petervflocke/ESP32Radio-V2PvF/Philips_DS1150/IMG20230203224731.jpg

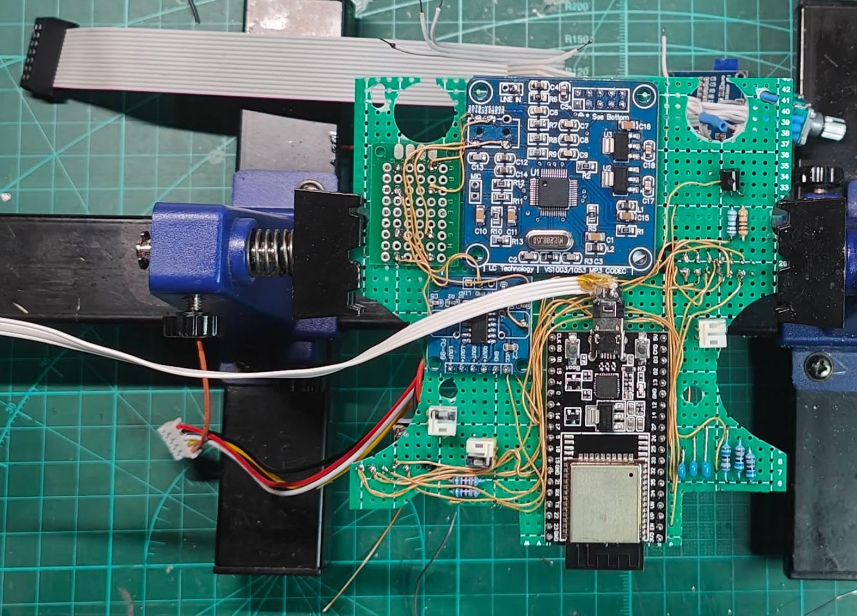
Philips_DS1150/IMG20230203224731.jpg
