petervflocke/ESP32Radio-V2PvF/Philips_DS1150/IMG20230203224739.jpg

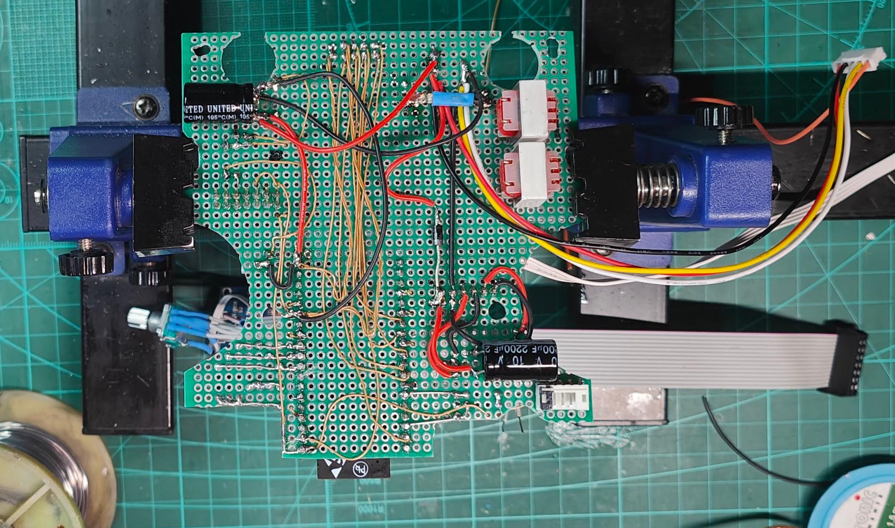
Philips_DS1150/IMG20230203224739.jpg
