petervflocke/ESP32Radio-V2PvF/Philips_DS1150/IMG20230204121923.jpg

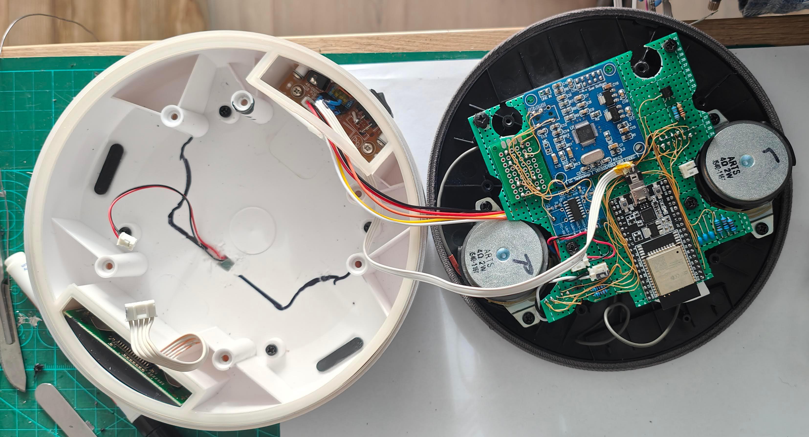
Philips_DS1150/IMG20230204121923.jpg
