petervflocke/ESP32Radio-V2PvF/Philips_DS1150/PhilipsESP32Radio.kicad_sch

## KiCad design Philips_DS1150/PhilipsESP32Radio.kicad_sch (2023-02-17)

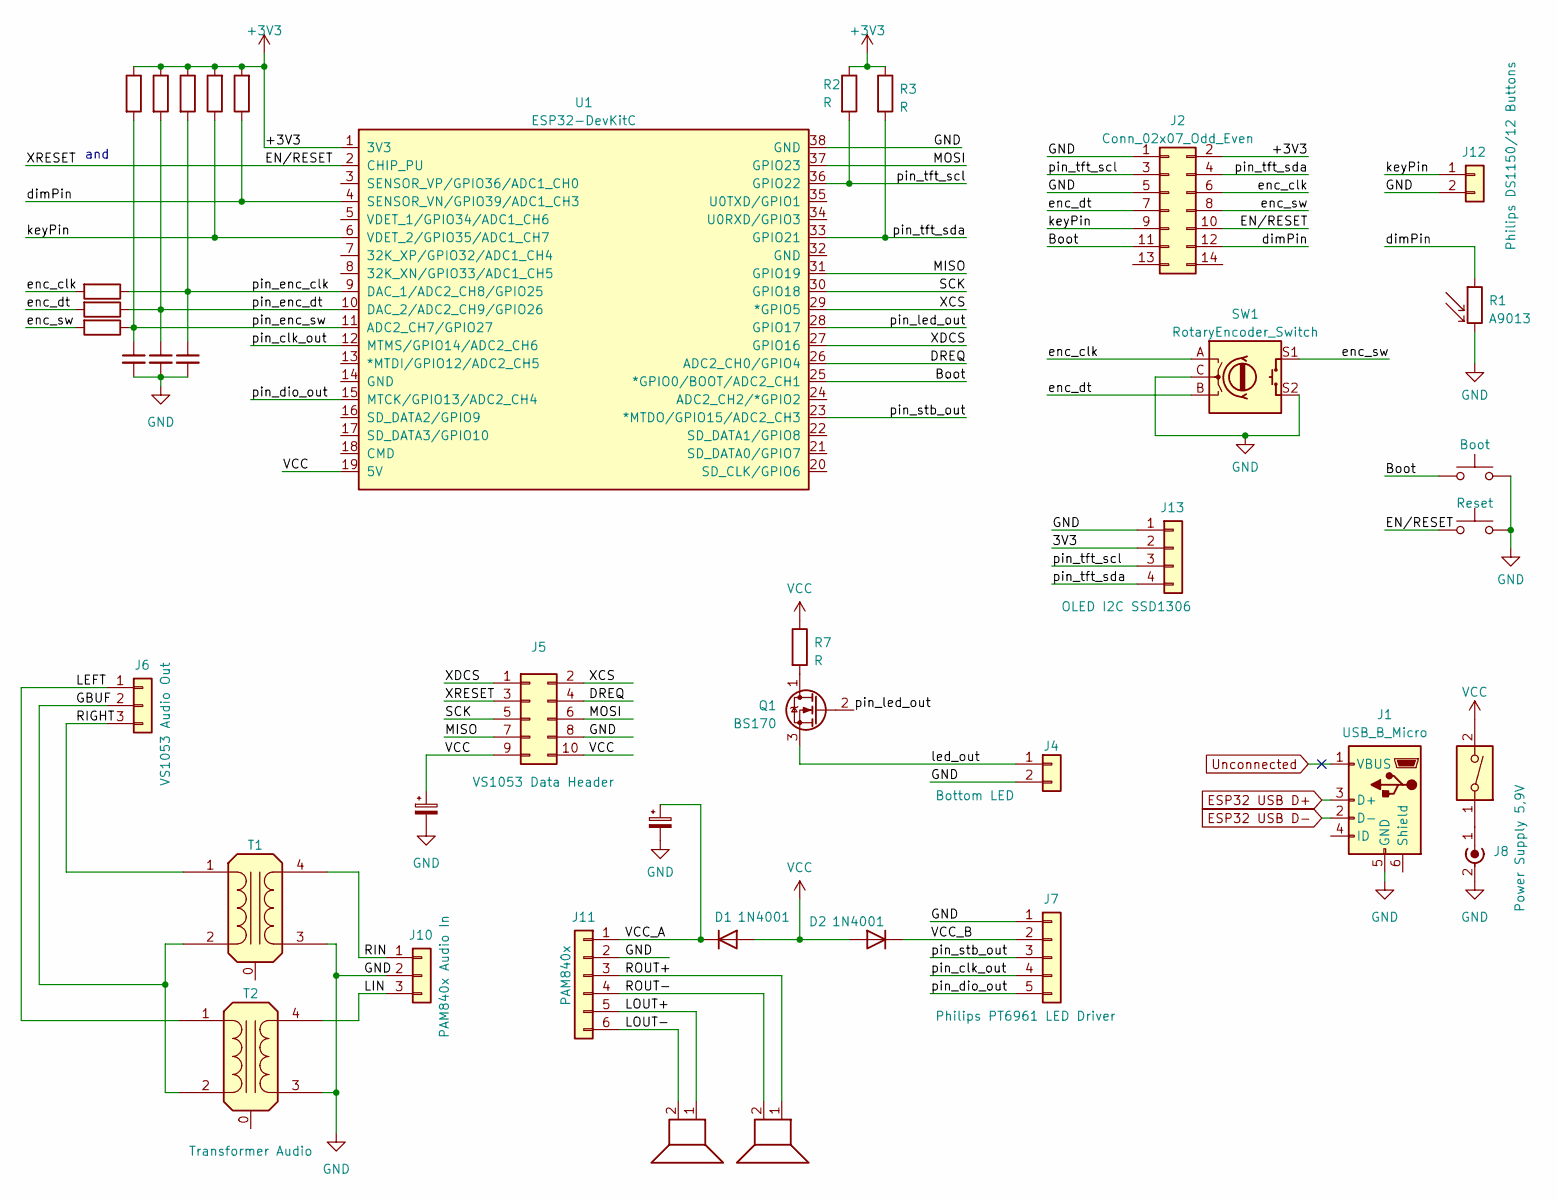
[picture p33: schematic PhilipsESP32Radio.kicad_sch]

Parts:
C1, C2, C3: C_Small
C4, C5: C_Polarized_Small
D1, D2: 1N4001; D_DO-41_SOD81_P10.16mm_Horizontal
J1: USB_B_Micro
J2: Conn_02x07_Odd_Even
J4: Bottom LED
J5: VS1053 Data Header
J6: VS1053 Audio Out
J7: Philips PT6961 LED Driver
J8: Power Supply 5,9V
J10: PAM840x Audio In
J11: PAM840x
J12: Philips DS1150/12 Buttons
J13: OLED I2C SSD1306
LS1, LS2: Speaker
Q1: BS170; TO-92_Inline
R1: A9013; R_LDR_5.0x4.1mm_P3mm_Vertical
R2, R3, R4, R5, R6, R7, R8, R9, R10, R11, R12: R
SW1: RotaryEncoder_Switch
SW2: Boot; SW_MEC_5GSH9
SW3: Reset; SW_MEC_5GSH9
SW4: SW_DIP_x01
T1: Transformer_Audio
T2: Transformer Audio
U1: ESP32-DevKitC

Connections:
3V3: J13.2
+3V3: J2.2, R2.1, R3.1, R8.2, R9.2, R10.1, R11.1, R12.1, U1.1 (3V3)
Boot: J2.11, SW2.1 (A), SW2.2 (A), U1.25 (*GPIO0/BOOT/ADC2_CH1)
DREQ: J5.4, U1.26 (ADC2_CH0/GPIO4)
EN/RESET: J2.10, J5.3, SW3.1 (A), SW3.2 (A), U1.2 (CHIP_PU)
ESP32 USB D+: J1.3 (D+)
ESP32 USB D-: J1.2 (D-)
GBUF: J6.2, T1.2 (AB), T2.2 (AB)
GND: C1.2, C2.2, C3.2, C4.2, C5.2, J1.5 (GND), J2.1, J2.5, J4.2, J5.8, J7.1, J8.2 (Ext), J10.2, J11.2, J12.2, J13.1, R1.2, SW1.C, SW1.S2, SW2.3 (B), SW2.4 (B), SW3.3 (B), SW3.4 (B), T1.3 (SA), T2.3 (SA), U1.38 (GND)
LEFT: J6.1, T2.1 (AA)
LIN: J10.3, T2.4 (SB)
LOUT+: J11.5, LS1.1
LOUT-: J11.6, LS1.2
MISO: J5.7, U1.31 (GPIO19)
MOSI: J5.6, U1.37 (GPIO23)
unnamed: J8.1 (In), SW4.1
unnamed: Q1.1 (D), R7.2
RIGHT: J6.3, T1.1 (AA)
RIN: J10.1, T1.4 (SB)
ROUT+: J11.3, LS2.1
ROUT-: J11.4, LS2.2
SCK: J5.5, U1.30 (GPIO18)
Unconnected: J1.1 (VBUS)
VCC: C5.1, D1.2 (A), D2.2 (A), J5.9, J5.10, R7.1, SW4.2, U1.19 (5V)
VCC_A: C4.1, D1.1 (K), J11.1
VCC_B: D2.1 (K), J7.2
XCS: J5.2, U1.29 (*GPIO5)
XDCS: J5.1, U1.27 (GPIO16)
dimPin: J2.12, R1.1, R9.1, U1.4 (SENSOR_VN/GPIO39/ADC1_CH3)
enc_clk: J2.6, R4.2, SW1.A
enc_dt: J2.7, R5.2, SW1.B
enc_sw: J2.8, R6.2, SW1.S1
keyPin: J2.9, J12.1, R8.1, U1.6 (VDET_2/GPIO35/ADC1_CH7)
led_out: J4.1, Q1.3 (S)
pin_clk_out: J7.4, U1.12 (MTMS/GPIO14/ADC2_CH6)
pin_dio_out: J7.5, U1.15 (MTCK/GPIO13/ADC2_CH4)
pin_enc_clk: C1.1, R4.1, R12.2, U1.9 (DAC_1/ADC2_CH8/GPIO25)
pin_enc_dt: C2.1, R5.1, R11.2, U1.10 (DAC_2/ADC2_CH9/GPIO26)
pin_enc_sw: C3.1, R6.1, R10.2, U1.11 (ADC2_CH7/GPIO27)
pin_led_out: Q1.2 (G), U1.28 (GPIO17)
pin_stb_out: J7.3
pin_stb_out: U1.23 (*MTDO/GPIO15/ADC2_CH3)
pin_tft_scl: J2.3, J13.3, R2.2, U1.36 (GPIO22)
pin_tft_sda: J2.4, J13.4, R3.2, U1.33 (GPIO21)

Notes on the sheet:
and
