petervflocke/ESP32Radio-V2PvF/src/main.cpp

//***************************************************************************************************
//*  ESP32_Radio V2 -- Webradio receiver for ESP32, VS1053 MP3 module and optional display.         *
//*                    By Ed Smallenburg.                                                           *
//***************************************************************************************************
// ESP32 libraries used:  See platformio.ini
// A library for the VS1053 (for ESP32) is not available (or not easy to find).  Therefore
// a class for this module is derived from the maniacbug library and integrated in this sketch.
// The Helix codecs for MP3 and HElix are taken from Wolle (schreibfaul1), see:
// https://github.com/schreibfaul1/ESP32-audioI2S
//
// See http://www.internet-radio.com for suitable stations.  Add the stations of your choice
// to the preferences through the webinterface.
// You may also use the "search" page of the webinterface to find stations.
//
// Brief description of the program:
// First a suitable WiFi network is found and a connection is made.
// Then a connection will be made to a shoutcast server.  The server starts with some
// info in the header in readable ascii, ending with a double CRLF, like:
//  icy-name:Classic Rock Florida - SHE Radio
//  icy-genre:Classic Rock 60s 70s 80s Oldies Miami South Florida
//  icy-url:http://www.ClassicRockFLorida.com
//  content-type:audio/mpeg
//  icy-pub:1
//  icy-metaint:32768          - Metadata after 32768 bytes of MP3-data
//  icy-br:128                 - in kb/sec (for Ogg this is like "icy-br=Quality 2"
//
// After de double CRLF is received, the server starts sending mp3- or Ogg-data.  For mp3, this
// data may contain metadata (non mp3) after every "metaint" mp3 bytes.
// The metadata is empty in most cases, but if any is available the content will be
// presented on the TFT.
// Pushing an input button causes the player to execute a programmable command.
//
// The display used is a Chinese 1.8 color TFT module 128 x 160 pixels.
// Now there is room for 26 characters per line and 16 lines.
// Software will work without installing the display.
// Other displays are also supported. See documentation.
// For configuration of the WiFi network(s): see the global data section further on.
//
// The VSPI interface is used for VS1053, TFT and SD.
//
// Wiring. Note that this is just an example.  Pins (except 18, 19 and 23 of the SPI interface)
// can be configured in the config page of the web interface.
//
// ESP32dev Signal  Wired to LCD        Wired to VS1053      AI Audio board    Wired to the rest
// -------- ------  --------------      -------------------  ---------------   ------------------------
// GPIO32           -                   pin 1 XDCS           I2C Clock
// GPIO33           -                   pin 1 XDCS           I2C Data
// GPIO5            -                   pin 2 XCS            KEY 6             -
// GPIO4            -                   pin 4 DREQ           AMPLIFIER_ENABLE  -
// GPIO2            pin 3 D/C or A0     -                    SPI_MISO          -
// GPIO16   RXD2    -                   -                                      TX of NEXTION (if in use)
// GPIO17   TXD2    -                   -                                      RX of NEXTION (if in use)
// GPIO18   SCK     pin 5 CLK or SCK    pin 5 SCK            KEY 5             -
// GPIO19   MISO    -                   pin 7 MISO           KEY 3             -
// GPIO23   MOSI    pin 4 DIN or SDA    pin 6 MOSI           KEY 4             -
// GPIO15           pin 2 CS            -                    SPI_MOSI          -
// GPIO3    RXD0    -                   -                                      Reserved serial input
// GPIO1    TXD0    -                   -                                      Reserved serial output
// GPIO34   -       -                   -                                      Optional pull-up resistor
// GPIO35   -       -                   -                                      Infrared receiver VS1838B
// GPIO25   -       -                   -                    I2S DSIN          Rotary encoder CLK
// GPIO26   -       -                   -                    I2S LRC           Rotary encoder DT
// GPIO27   -       -                   -                    I2S BCLK          Rotary encoder SW
// GPIO13   -       -                   -                    SD card CS        -
// GPIO14   -       -                   -                    SPI_SCK           -
// GPIO36   -       -                   -                    KEY 1             -
// GPIO13   -       -                   -                    KEY 2             -
// GPIO19   -       -                   -                    KEY 3             -
// GPIO23   -       -                   -                    KEY 4             -
// GPIO18   -       -                   -                    KEY 5             -
// GPIO05   -       -                   -                    KEY 6             -
// -------  ------  ---------------     -------------------                    ----------------
// GND      -       pin 8 GND           pin 8 GND                              Power supply GND
// VCC 5 V  -       pin 7 BL            -                                      Power supply
// VCC 5 V  -       pin 6 VCC           pin 9 5V                               Power supply
// EN       -       pin 1 RST           pin 3 XRST                             -
//
//  History:
//   Date     Author        Remarks
// ----------  --  ------------------------------------------------------------------
// 06-08-2021, ES: Copy from version 1.
// 06-08-2021, ES: Use SPIFFS and Async webserver.
// 23-08-2021, ES: Version with software MP3/AAC decoders.
// 05-10-2021, ES: Fixed internal DAC output, fixed OTA update.
// 06-10-2021, ES: Fixed AP mode.
// 10-02-2022, ES: Included ST7789 display.
// 11-02-2022, ES: SD card implementation.
// 26-03-2022, ES: Fixed NEXTION bug.
// 12-04-2022, ES: Fixed dataqueue bug (NEXT function).
// 13-04-2022, ES: Fixed redirect bug (preset was reset), fixed playlist.
// 14-04-2022, ES: Added posibility for a fixed WiFi network.
// 15-04-2022, ES: Redesigned station selection.
// 25-04-2022, ES: Support for WT32-ETH01 (wired Ethernet).
// 13-05-2022, ES: Correction I2S settings.
// 15-05-2022, ES: Correction mp3 list for web interface.
// 01-11-2022, ES: Support of AI Audio kit V2.1.
//
// Define the version number, the format used is the HTTP standard.
//#define VERSION     "Thu, 03 Nov 2022 13:00:00 GMT"     
#define VERSION "V2.1"                                    // just the PvF version
const char version[] = VERSION " " __DATE__;              // PvF prefers to have the last compilation time

#include <Arduino.h>                                      // Standard include for Platformio Arduino projects
#include <WiFi.h>
#include "config.h"                                       // Specify display type, decoder type
#include <nvs.h>                                          // Access to NVS
#include <PubSubClient.h>                                 // MTTQ access
#ifdef ETHERNET
  // Definitions for Ethernet controller
  #include <ETH.h>
  #define ETH_CLK_MODE    ETH_CLOCK_GPIO0_IN              // External clock from crystal oscillator
  #define ETH_TYPE        ETH_PHY_LAN8720                 // Type of controller
  #define ETH_ADDR        1                               // I2C address of Ethernet PHY
#else
  #include <WiFiMulti.h>                                  // Handle multiple WiFi networks
  WiFiMulti wifiMulti ;                                   // Object for WiFiMulti
#endif
#include <ESPmDNS.h>                                      // For multicast DNS
#include <time.h>                                         // Time functions
#include <SPI.h>                                          // For SPI handling
#include <ArduinoOTA.h>                                   // Over the air updates
#include <ESPAsyncWebServer.h>                            // For Async Web server
#include <freertos/queue.h>                               // FreeRtos queue support
#include <freertos/task.h>                                // FreeRtos task handling
#include <driver/adc.h>                                   // ADC driver
#include <base64.h>                                       // For Basic authentication
#include <SPIFFS.h>                                       // Filesystem
#include "utils.h"                                        // Some handy utilities

#ifdef FIDELO
  #include "fidelio_display.h"
  #define spiClk 1000000UL 
  #define dimPin 39
  #define keyPin 35
  #define NoAnalogButtonPressed 4000 /* actually 4095; maximum value ADC reading connected to 3.3V */
  
  FidelioDisplay fideDisplay;
#endif

/* Philips Fildelio Resistance Key Pin values measured with 3kohm pullup to 3.3v
1. clock :    0 -  100
2. +     :  470 -  530
3. light : 1060 - 1120
4. -     : 2220 - 2280
not pressed anything bigger then 2280
*/


#if defined(DEC_HELIX_INT) || defined(DEC_HELIX_AI)       // Software decoder using internal DAC?
  #define DEC_HELIX                                       // Yes, make sure to include software decoders
  #ifdef DEC_HELIX_AI                                     // AI Audio kit board?
   #include <AC101.h>
   #define GPIO_PA_EN 21                                  // GPIO for enabling amplifier
   AC101 dac ;                                            // AC101 controls
  #endif
#endif
#ifdef DEC_HELIX                                          // Software decoder?
  #include <driver/i2s.h>                                 // Driver for I2S output
  #include "mp3_decoder.h"                                // Yes, include libhelix_HMP3DECODER
  #include "aac_decoder.h"                                // and libhelix_HAACDECODER
  #include "helixfuncs.h"                                 // Helix functions
#else
  #include "VS1053.h"                                     // Driver for VS1053
#endif
#define FSIF              true                            // Format SPIFFS if not existing
#define QSIZ              400                             // Number of entries in the queue
#define NVSBUFSIZE        150                             // Max size of a string in NVS
// Access point name if connection to WiFi network fails.  Also the hostname for WiFi and OTA.
// Note that the password of an AP must be at least as long as 8 characters.
// Also used for other naming.
#ifndef NAME                                              // Name may be defined in config.h
  #define NAME            "ESP32-Radio"
#endif
#define MAXPRESETS        200                             // Max number of presets in preferences
#define MAXMQTTCONNECTS   5                               // Maximum number of MQTT reconnects before give-up
#define METASIZ           1024                            // Size of metaline buffer
#define MAXKEYS           200                             // Max. number of NVS keys in table
#define BL_TIME           45                              // Time-out [sec] for blanking TFT display (BL pin)
//
// Subscription topics for MQTT.  The topic will be pefixed by "PREFIX/", where PREFIX is replaced
// by the the mqttprefix in the preferences.  The next definition will yield the topic
// "ESP32Radio/command" if mqttprefix is "ESP32Radio".
#define MQTT_SUBTOPIC     "command"                      // Command to receive from MQTT
//
#define heapspace heap_caps_get_largest_free_block ( MALLOC_CAP_8BIT )

//**************************************************************************************************
// Forward declaration and prototypes of various functions.                                        *
//**************************************************************************************************
void        tftlog ( const char *str, bool newline = false ) ;
void        otastart() ;
void        showstreamtitle ( const char* ml, bool full = false ) ;
void        handlebyte_ch ( uint8_t b ) ;
void        handleCmd()  ;
const char* analyzeCmd ( const char* str ) ;
const char* analyzeCmd ( const char* par, const char* val ) ;
void        chomp ( String &str ) ;
String      nvsgetstr ( const char* key ) ;
bool        nvssearch ( const char* key ) ;
void        sdfuncs() ;
void        stop_mp3client () ;
void        tftset ( uint16_t inx, const char *str ) ;
void        tftset ( uint16_t inx, String& str ) ;
void        playtask ( void* parameter ) ;             // Task to play the stream on VS1053 or HELIX decoder
void        displayinfo ( uint16_t inx ) ;
void        gettime() ;
void        reservepin ( int8_t rpinnr ) ;
void        claimSPI ( const char* p ) ;                // Claim SPI bus for exclusive access
void        releaseSPI() ;                              // Release the claim
uint32_t    ssconv ( const uint8_t* bytes ) ;
void        scan_content_length ( const char* metalinebf ) ;
void        handle_notfound  ( AsyncWebServerRequest *request ) ;
void        handle_getprefs  ( AsyncWebServerRequest *request ) ;
void        handle_saveprefs ( AsyncWebServerRequest *request ) ;
void        handle_getdefs   ( AsyncWebServerRequest *request ) ;
void        handle_settings  ( AsyncWebServerRequest *request ) ;
void        handle_mp3list   ( AsyncWebServerRequest *request ) ;
String      readhostfrompref ( int16_t preset ) ;
void        displayStop();
bool        getPresetName (int16_t presetId, String &str);  // check if icy or preset name shall be used
#ifdef SCANANALOG
void        scananalog(); // scaning Philips
#endif


//**************************************************************************************************
// Several structs and enums.                                                                      *
//**************************************************************************************************
//

enum qdata_type { QDATA, QSTARTSONG, QSTOPSONG,       // datatyp in qdata_struct,
                  QSTOPTASK } ;
struct qdata_struct                                   // Data in queue for playtask (dataqueue)
{
  qdata_type                          datatyp ;       // Identifier
  __attribute__((aligned(4))) uint8_t buf[32] ;       // Buffer for chunk of mp3 data
} ;

struct ini_struct
{
  String         mqttbroker ;                         // The name of the MQTT broker server
  String         mqttprefix ;                         // Prefix to use for topics
  uint16_t       mqttport ;                           // Port, default 1883
  String         mqttuser ;                           // User for MQTT authentication
  String         mqttpasswd ;                         // Password for MQTT authentication
  uint8_t        reqvol ;                             // Requested volume
  uint8_t        rtone[4] ;                           // Requested bass/treble settings
  String         clk_server ;                         // Server to be used for time of day clock
  int8_t         clk_offset ;                         // Offset in hours with respect to UTC
  int8_t         clk_dst ;                            // Number of hours shift during DST
  int8_t         ir_pin ;                             // GPIO connected to output of IR decoder
  int8_t         enc_clk_pin ;                        // GPIO connected to CLK of rotary encoder
  int8_t         enc_dt_pin ;                         // GPIO connected to DT of rotary encoder
  int8_t         enc_sw_pin ;                         // GPIO connected to SW of rotary encoder / ZIPPY B5
  int8_t         enc_up_pin ;                         // GPIO connected to UP of ZIPPY B5 side switch
  int8_t         enc_dwn_pin ;                        // GPIO connected to DOWN of ZIPPY B5 side switch
  int8_t         tft_cs_pin ;                         // GPIO connected to CS of TFT screen
  int8_t         tft_dc_pin ;                         // GPIO connected to D/C or A0 of TFT screen
  int8_t         tft_scl_pin ;                        // GPIO connected to SCL of i2c TFT screen
  int8_t         tft_sda_pin ;                        // GPIO connected to SDA of I2C TFT screen
  int8_t         tft_bl_pin ;                         // GPIO to activate BL of display
  int8_t         tft_blx_pin ;                        // GPIO to activate BL of display (inversed logic)
  int8_t         nxt_rx_pin ;                         // GPIO for input from NEXTION
  int8_t         nxt_tx_pin ;                         // GPIO for output to NEXTION
  int8_t         sd_cs_pin ;                          // GPIO connected to CS of SD card
  int8_t         vs_cs_pin ;                          // GPIO connected to CS of VS1053
  int8_t         vs_dcs_pin ;                         // GPIO connected to DCS of VS1053
  int8_t         vs_dreq_pin ;                        // GPIO connected to DREQ of VS1053
  int8_t         shutdown_pin ;                       // GPIO to shut down the amplifier
  int8_t         shutdownx_pin ;                      // GPIO to shut down the amplifier (inversed logic)
  int8_t         spi_sck_pin ;                        // GPIO connected to SPI SCK pin
  int8_t         spi_miso_pin ;                       // GPIO connected to SPI MISO pin
  int8_t         spi_mosi_pin ;                       // GPIO connected to SPI MOSI pin
  int8_t         i2s_bck_pin ;                        // GPIO Pin number for I2S "BCK"
  int8_t         i2s_lck_pin ;                        // GPIO Pin number for I2S "L(R)CK"
  int8_t         i2s_din_pin ;                        // GPIO Pin number for I2S "DIN"
  int8_t         eth_mdc_pin ;                        // GPIO Pin number for Ethernet controller MDC
  int8_t         eth_mdio_pin ;                       // GPIO Pin number for Ethernet controller MDIO
  int8_t         eth_power_pin ;                      // GPIO Pin number for Ethernet controller POWER
  uint16_t       bat0 ;                               // ADC value for 0 percent battery charge
  uint16_t       bat100 ;                             // ADC value for 100 percent battery charge
  int8_t         pin_led_out;                         // PvF: GPIO out Pin for bottom LED driver
  int8_t         pin_stb_out;                         // PvF: GPIO out STB  Fidelo Display PT6964
  int8_t         pin_clk_out;                         // PvF: GPIO out CLK  Fidelo Display PT6964
  int8_t         pin_dio_out;                         // PvF: GPIO out DI/O Fidelo Display PT6964

} ;

struct WifiInfo_t                                     // For list with WiFi info
{
  char * ssid ;                                       // SSID for an entry
  char * passphrase ;                                 // Passphrase for an entry
} ;

struct nvs_entry
{
  uint8_t  Ns ;                                       // Namespace ID
  uint8_t  Type ;                                     // Type of value
  uint8_t  Span ;                                     // Number of entries used for this item
  uint8_t  Rvs ;                                      // Reserved, should be 0xFF
  uint32_t CRC ;                                      // CRC
  char     Key[16] ;                                  // Key in Ascii
  uint64_t Data ;                                     // Data in entry
} ;

struct nvs_page                                       // For nvs entries
{ // 1 page is 4096 bytes
  uint32_t  State ;
  uint32_t  Seqnr ;
  uint32_t  Unused[5] ;
  uint32_t  CRC ;
  uint8_t   Bitmap[32] ;
  nvs_entry Entry[126] ;
} ;

struct keyname_t                                      // For keys in NVS
{
  char      Key[16] ;                                 // Max length is 15 plus delimeter
} ;

// Preset info
enum station_state_t { ST_PRESET, ST_REDIRECT,        // Possible preset status
                       ST_PLAYLIST, ST_STATION } ;
struct preset_info_t
{
    int16_t            preset ;                       // Preset to play
    int16_t            highest_preset ;               // Highest possible preset
    station_state_t    station_state ;                // Station state
    int16_t            playlistnr ;                   // Index in playlist
    int16_t            highest_playlistnr ;           // Highest possible preset
    String             playlisthost ;                 // Host with playlist
    String             host ;                         // Resulting host
} ;


//**************************************************************************************************
// Global data section.                                                                            *
//**************************************************************************************************
// There is a block ini-data that contains some configuration.  Configuration data is              *
// saved in the preferences by the webinterface.  On restart the new data will                     *
// de read from these preferences.                                                                 *
// Items in ini_block can be changed by commands from webserver/MQTT/Serial.                       *
//**************************************************************************************************

enum datamode_t { INIT = 0x1, HEADER = 0x2, DATA = 0x4,      // State for datastream
                  METADATA = 0x8, PLAYLISTINIT = 0x10,
                  PLAYLISTHEADER = 0x20, PLAYLISTDATA = 0x40,
                  STOPREQD = 0x80, STOPPED = 0x100
                } ;

// Global variables
int               numSsid ;                              // Number of available WiFi networks
bool              ota = true ;                           // Allow OTA updates
preset_info_t     presetinfo ;                           // Info about the current or new station
ini_struct        ini_block ;                            // Holds configurable data
AsyncWebServer    cmdserver ( 80 ) ;                     // Instance of embedded webserver, port 80
AsyncClient*      mp3client = NULL ;                     // An instance of the mp3 client
WiFiClient        wmqttclient ;                          // An instance for mqtt
PubSubClient      mqttclient ( wmqttclient ) ;           // Client for MQTT subscriber
TaskHandle_t      maintask ;                             // Taskhandle for main task
TaskHandle_t      xplaytask ;                            // Task handle for playtask
SemaphoreHandle_t SPIsem = NULL ;                        // For exclusive SPI usage
hw_timer_t*       timer = NULL ;                         // For timer
char              timetxt[9] ;                           // Converted timeinfo
char              cmd[130] ;                             // Command from MQTT or Serial
const qdata_type  stopcmd = QSTOPSONG ;                  // Command for radio/SD
const qdata_type  startcmd = QSTARTSONG ;                // Command for radio/SD
QueueHandle_t     radioqueue = 0 ;                       // Queue for icecast commands
QueueHandle_t     dataqueue = 0 ;                        // Queue for mp3 datastream
QueueHandle_t     sdqueue = 0 ;                          // For commands to sdfuncs
qdata_struct      outchunk ;                             // Data to queue
qdata_struct      inchunk ;                              // Data from queue
uint8_t*          outqp = outchunk.buf ;                 // Pointer to buffer in outchunk
uint32_t          totalcount = 0 ;                       // Counter mp3 data
datamode_t        datamode ;                             // State of datastream
int               metacount ;                            // Number of bytes in metadata
int               datacount ;                            // Counter databytes before metadata
char              metalinebf[METASIZ + 1] ;              // Buffer for metaline/ID3 tags
int16_t           metalinebfx ;                          // Index for metalinebf
String            icystreamtitle ;                       // Streamtitle from metadata
String            icyname ;                              // Icecast station name
String            audio_ct ;                             // Content-type, like "audio/aacp"
String            ipaddress ;                            // Own IP-address
int               bitrate ;                              // Bitrate in kb/sec
int               mbitrate ;                             // Measured bitrate
int               metaint = 0 ;                          // Number of databytes between metadata
bool              reqtone = false ;                      // New tone setting requested
bool              muteflag = false ;                     // Mute output
bool              resetreq = false ;                     // Request to reset the ESP32
bool              testreq = false ;                      // Request to print test info
bool              eth_connected = false ;                // Ethernet connected or not
bool              NetworkFound = false ;                 // True if WiFi network connected
bool              mqtt_on = false ;                      // MQTT in use
String            networks = "None|" ;                   // Found networks in the surrounding
uint16_t          mqttcount = 0 ;                        // Counter MAXMQTTCONNECTS
int8_t            playingstat = 0 ;                      // 1 if radio is playing (for MQTT)
int16_t           playlist_num = 0 ;                     // Nonzero for selection from playlist
bool              chunked = false ;                      // Station provides chunked transfer
int               chunkcount = 0 ;                       // Counter for chunked transfer
uint16_t          ir_value = 0 ;                         // IR code
uint32_t          ir_0 = 550 ;                           // Average duration of an IR short pulse
uint32_t          ir_1 = 1650 ;                          // Average duration of an IR long pulse
struct tm         timeinfo ;                             // Will be filled by NTP server
bool              time_req = false ;                     // Set time requested
uint16_t          adcvalraw ;                            // ADC value (raw)
uint16_t          adcval ;                               // ADC value (battery voltage, averaged)
uint32_t          clength ;                              // Content length found in http header
uint16_t          bltimer = 0 ;                          // Backlight time-out counter
bool              dsp_ok = false ;                       // Display okay or not
int               ir_intcount = 0 ;                      // For test IR interrupts
bool              spftrigger = false ;                   // To trigger execution of special functions
const char*       fixedwifi = "" ;                       // Used for FIXEDWIFI option
const esp_partition_t*  spiffs = NULL ;                  // Pointer to SPIFFS partition struct
std::vector<WifiInfo_t> wifilist ;                       // List with wifi_xx info

// nvs stuff
nvs_page                nvsbuf ;                         // Space for 1 page of NVS info
const esp_partition_t*  nvs ;                            // Pointer to partition struct
esp_err_t               nvserr ;                         // Error code from nvs functions
uint32_t                nvshandle = 0 ;                  // Handle for nvs access
uint8_t                 namespace_ID ;                   // Namespace ID found
char                    nvskeys[MAXKEYS][16] ;           // Space for NVS keys
std::vector<keyname_t>  keynames ;                       // Keynames in NVS

// Rotary encoder stuff
#define sv DRAM_ATTR static volatile
sv uint16_t       clickcount = 0 ;                       // Incremented per encoder click
sv int16_t        rotationcount = 0 ;                    // Current position of rotary switch
sv uint16_t       enc_inactivity = 0 ;                   // Time inactive
sv bool           singleclick = false ;                  // True if single click detected
sv bool           doubleclick = false ;                  // True if double click detected
sv bool           tripleclick = false ;                  // True if triple click detected
sv bool           longclick = false ;                    // True if longclick detected
enum enc_menu_t { VOLUME, PRESET, TRACK };    // State for rotary encoder menu, OFF for new toggle comand
enc_menu_t        enc_menu_mode = VOLUME ;               // Default is VOLUME mode

//
struct progpin_struct                                    // For programmable input pins
{
  int8_t         gpio ;                                  // Pin number
  bool           reserved ;                              // Reserved for connected devices
  bool           avail ;                                 // Pin is available for a command
  String         command ;                               // Command to execute when activated
                                                         // Example: "uppreset=1"
  bool           cur ;                                   // Current state, true = HIGH, false = LOW
} ;

progpin_struct   progpin[] =                             // Input pins and programmed function
{
  {  0, false, false,  "", false },
  //{  1, true,  false,  "", false },                    // Reserved for TX Serial output
  {  2, false, false,  "", false },
  //{  3, true,  false,  "", false },                    // Reserved for RX Serial input
  {  4, false, false,  "", false },
  {  5, false, false,  "", false },
  //{  6, true,  false,  "", false },                    // Reserved for FLASH SCK
  //{  7, true,  false,  "", false },                    // Reserved for FLASH D0
  //{  8, true,  false,  "", false },                    // Reserved for FLASH D1
  //{  9, true,  false,  "", false },                    // Reserved for FLASH D2
  //{ 10, true,  false,  "", false },                    // Reserved for FLASH D3
  //{ 11, true,  false,  "", false },                    // Reserved for FLASH CMD
  { 12, false, false,  "", false },
  { 13, false, false,  "", false },
  { 14, false, false,  "", false },
  { 15, false, false,  "", false },
  { 16, false, false,  "", false },                      // May be UART 2 RX for Nextion
  { 17, false, false,  "", false },                      // May be UART 2 TX for Nextion
  { 18, false, false,  "", false },                      // Default for SPI CLK
  { 19, false, false,  "", false },                      // Default for SPI MISO
  //{ 20, true,  false,  "", false },                    // Not exposed on DEV board
  { 21, false, false,  "", false },                      // Also Wire SDA
  { 22, false, false,  "", false },                      // Also Wire SCL
  { 23, false, false,  "", false },                      // Default for SPI MOSI
  //{ 24, true,  false,  "", false },                    // Not exposed on DEV board
  { 25, false, false,  "", false },                      // DAC output / I2S output
  { 26, false, false,  "", false },                      // DAC output / I2S output
  { 27, false, false,  "", false },                      // I2S output
  //{ 28, true,  false,  "", false },                    // Not exposed on DEV board
  //{ 29, true,  false,  "", false },                    // Not exposed on DEV board
  //{ 30, true,  false,  "", false },                    // Not exposed on DEV board
  //{ 31, true,  false,  "", false },                    // Not exposed on DEV board
  { 32, false, false,  "", false },
  { 33, false, false,  "", false },
  { 34, false, false,  "", false },                      // Note, no internal pull-up
  //{ 35, true, false,  "", false },                     // Fidelio 4 keys resitor based
  //{ 36, true,  false,  "", false },                    // Reserved for ADC battery level
  //{ 39, true,  false,  "", false },                    // Light sensor for Fidelio Display
  { -1, false, false,  "", false }                       // End of list
} ;

#ifdef SCANDIGITAl
struct touchpin_struct                                   // For programmable input pins
{
  int8_t         gpio ;                                  // Pin number GPIO
  bool           reserved ;                              // Reserved for connected devices
  bool           avail ;                                 // Pin is available for a command
  String         command ;                               // Command to execute when activated
                                                         // Example: "uppreset=1"
  bool           cur ;                                   // Current state, true = HIGH, false = LOW
  int16_t        count ;                                 // Counter number of times low level
} ;

touchpin_struct   touchpin[] =                           // Touch pins and programmed function
{
  {   4, false, false, "", false, 0 },                   // TOUCH0
  {   0, true,  false, "", false, 0 },                   // TOUCH1, reserved for BOOT button
  {   2, false, false, "", false, 0 },                   // TOUCH2
  {  15, false, false, "", false, 0 },                   // TOUCH3
  {  13, false, false, "", false, 0 },                   // TOUCH4
  {  12, false, false, "", false, 0 },                   // TOUCH5
  {  14, false, false, "", false, 0 },                   // TOUCH6
  {  27, false, false, "", false, 0 },                   // TOUCH7
  {  33, false, false, "", false, 0 },                   // TOUCH8
  {  32, false, false, "", false, 0 },                   // TOUCH9
  {  -1, false, false, "", false, 0 }                    // End of list
  // End of table
} ;
#endif

#ifdef SCANANALOG
// PvF analog scan structure
struct analogpin_struct                                 // PvF: For programmable analog input pin
{                                                       //      of resitor ladder
  int8_t        commandNumber;                          // Pin number GPIO
  uint16_t      minValue ;                              // min value detected by pressed button
  bool          avail ;                                 // Pin is available for a command
  String        command ;                               // Command to execute when activated
                                                        // Example: "uppreset=1"
  bool          cur ;                                   // Current state, true = HIGH, false = LOW
  int8_t        last_cmd;                               // Counter number of times low level
} ;

#define NumButtons 4  /* excluding the last one status for unpressed */
analogpin_struct   analogpin[] =              // Touch pins and programmed function
// All pins are not available as long as they are not defined in the preferences
{
  {   0,  100, false, "", false, 0 },                   // clock    
  {   1,  800, false, "", false, 0 },                   // +
  {   2, 1500, false, "", false, 0 },                   // light
  {   3, 2500, false, "", false, 0 },                   // -
  {  -1,    0, false, "", false, 0 }                    // End of list
  // End of table
} ;
#endif

// Actualy not only for Fidelio, can be used for any connetced PWM LED 
// bottom leds PWM value                                 // Fidelio bottom LEDs
#define MAXPWMIDX 4
u_int8_t PWMValue[] = {0, 40, 128, 255};                 // possible LED PWM values
u_int8_t PWMidx = 0;                                     // brightnes' index 


//**************************************************************************************************
// End of global data section.                                                                     *
//**************************************************************************************************




//**************************************************************************************************
//                                     M Q T T P U B _ C L A S S                                   *
//**************************************************************************************************
// ID's for the items to publish to MQTT.  Is index in amqttpub[]
enum { MQTT_IP,     MQTT_ICYNAME, MQTT_STREAMTITLE, MQTT_NOWPLAYING,
       MQTT_PRESET, MQTT_VOLUME, MQTT_PLAYING, MQTT_PLAYLISTPOS
     } ;
enum { MQSTRING, MQINT8, MQINT16 } ;                     // Type of variable to publish

class mqttpubc                                           // For MQTT publishing
{
    struct mqttpub_struct
    {
      const char*    topic ;                             // Topic as partial string (without prefix)
      uint8_t        type ;                              // Type of payload
      void*          payload ;                           // Payload for this topic
      bool           topictrigger ;                      // Set to true to trigger MQTT publish
    } ;
    // Publication topics for MQTT.  The topic will be pefixed by "PREFIX/", where PREFIX is replaced
    // by the the mqttprefix in the preferences.
  protected:
    mqttpub_struct amqttpub[9] =                         // Definitions of various MQTT topic to publish
    { // Index is equal to enum above
      { "ip",              MQSTRING, &ipaddress,             false }, // Definition for MQTT_IP
      { "icy/name",        MQSTRING, &icyname,               false }, // Definition for MQTT_ICYNAME
      { "icy/streamtitle", MQSTRING, &icystreamtitle,        false }, // Definition for MQTT_STREAMTITLE
      { "nowplaying",      MQSTRING, &ipaddress,             false }, // Definition for MQTT_NOWPLAYING
      { "preset" ,         MQINT8,   &presetinfo.preset,     false }, // Definition for MQTT_PRESET
      { "volume" ,         MQINT8,   &ini_block.reqvol,      false }, // Definition for MQTT_VOLUME
      { "playing",         MQINT8,   &playingstat,           false }, // Definition for MQTT_PLAYING
      { "playlist/pos",    MQINT16,  &presetinfo.playlistnr, false }, // Definition for MQTT_PLAYLISTPOS
      { NULL,              0,        NULL,                   false }  // End of definitions
    } ;
  public:
    void          trigger ( uint8_t item ) ;                      // Trigger publishig for one item
    void          publishtopic() ;                                // Publish triggerer items
} ;


//**************************************************************************************************
// MQTTPUB  class implementation.                                                                  *
//**************************************************************************************************

//**************************************************************************************************
//                                            T R I G G E R                                        *
//**************************************************************************************************
// Set request for an item to publish to MQTT.                                                     *
//**************************************************************************************************
void mqttpubc::trigger ( uint8_t item )                    // Trigger publishig for one item
{
  amqttpub[item].topictrigger = true ;                     // Request re-publish for an item
}

//**************************************************************************************************
//                                     P U B L I S H T O P I C                                     *
//**************************************************************************************************
// Publish a topic to MQTT broker.                                                                 *
//**************************************************************************************************
void mqttpubc::publishtopic()
{
  int         i = 0 ;                                         // Loop control
  char        topic[80] ;                                     // Topic to send
  const char* payload ;                                       // Points to payload
  char        intvar[10] ;                                    // Space for integer parameter

  while ( amqttpub[i].topic )
  {
    if ( amqttpub[i].topictrigger )                           // Topic ready to send?
    {
      amqttpub[i].topictrigger = false ;                      // Success or not: clear trigger
      sprintf ( topic, "%s/%s", ini_block.mqttprefix.c_str(),
                amqttpub[i].topic ) ;                         // Add prefix to topic
      switch ( amqttpub[i].type )                             // Select conversion method
      {
        case MQSTRING :
          payload = ((String*)amqttpub[i].payload)->c_str() ;
          //payload = pstr->c_str() ;                           // Get pointer to payload
          break ;
        case MQINT8 :
          sprintf ( intvar, "%d",
                    *(int8_t*)amqttpub[i].payload ) ;         // Convert to array of char
          payload = intvar ;                                  // Point to this array
          break ;
        case MQINT16 :
          sprintf ( intvar, "%d",
                    *(int16_t*)amqttpub[i].payload ) ;        // Convert to array of char
          payload = intvar ;                                  // Point to this array
          break ;
        default :
          continue ;                                          // Unknown data type
      }
      dbgprint ( "Publish to topic %s : %s",                  // Show for debug
                 topic, payload ) ;
      if ( !mqttclient.publish ( topic, payload ) )           // Publish!
      {
        dbgprint ( "MQTT publish failed!" ) ;                 // Failed
      }
      return ;                                                // Do the rest later
    }
    i++ ;                                                     // Next entry
  }
}

mqttpubc         mqttpub ;                                    // Instance for mqttpubc

//
// Include software for the right display
#ifdef BLUETFT
 #include "bluetft.h"                                        // For ILI9163C or ST7735S 128x160 display
#endif
#ifdef ST7789
 #include "ST7789.h"                                         // For ST7789 240x240 display
#endif
#ifdef ILI9341
 #include "ILI9341.h"                                        // For ILI9341 320x240 display
#endif
#ifdef OLED1306
 #include "oled.h"                                           // For OLED I2C SD1306 64x128 display
#endif
#ifdef OLED1309
 #include "oled.h"                                           // For OLED I2C SD1309 64x128 display
#endif
#ifdef OLED1106
 #include "oled.h"                                           // For OLED I2C SH1106 64x128 display
#endif
#ifdef LCD1602I2C
 #include "LCD1602.h"                                        // For LCD 1602 display (I2C)
#endif
#ifdef LCD2004I2C
 #include "LCD2004.h"                                        // For LCD 2004 display (I2C)
#endif
#ifdef DUMMYTFT
 #include "dummytft.h"                                       // For Dummy display
#endif
#ifdef NEXTION
 #include "NEXTION.h"                                        // For NEXTION display
#endif

// Include software for SD card.  Will include dummy if "SDCARD" is not defined
#include "SDcard.h"                                         // For SD card interface

//**************************************************************************************************
//                                  M Y Q U E U E S E N D                                          *
//**************************************************************************************************
// Send to queue if existing.                                                                      *
//**************************************************************************************************
void myQueueSend ( QueueHandle_t q, const void* msg, int waittime = 0 )
{
  if ( q )                                                // Check if we have a legal queue
  {
    xQueueSend ( q, msg, waittime ) ;                     // Queue okay, send to it
  }
}


//**************************************************************************************************
//                                           B L S E T                                             *
//**************************************************************************************************
// Enable or disable the TFT backlight if configured.                                              *
// May be called from interrupt level.                                                             *
//**************************************************************************************************
void IRAM_ATTR blset ( bool enable )
{
  if ( ini_block.tft_bl_pin >= 0 )                       // Backlight for TFT control?
  {
    digitalWrite ( ini_block.tft_bl_pin, enable ) ;      // Enable/disable backlight
  }
  if ( ini_block.tft_blx_pin >= 0 )                      // Backlight for TFT (inversed logic) control?
  {
    digitalWrite ( ini_block.tft_blx_pin, !enable ) ;    // Enable/disable backlight
  }
  if ( enable )
  {
    bltimer = 0 ;                                        // Reset counter backlight time-out
  }
}


//**************************************************************************************************
//                                      N V S O P E N                                              *
//**************************************************************************************************
// Open Preferences with my-app namespace. Each application module, library, etc.                  *
// has to use namespace name to prevent key name collisions. We will open storage in               *
// RW-mode (second parameter has to be false).                                                     *
//**************************************************************************************************
void nvsopen()
{
  if ( ! nvshandle )                                         // Opened already?
  {
    nvserr = nvs_open ( NAME, NVS_READWRITE, &nvshandle ) ;  // No, open nvs
    if ( nvserr )
    {
      dbgprint ( "nvs_open failed!" ) ;
    }
  }
}


//**************************************************************************************************
//                                      N V S C L E A R                                            *
//**************************************************************************************************
// Clear all preferences.                                                                          *
//**************************************************************************************************
esp_err_t nvsclear()
{
  nvsopen() ;                                         // Be sure to open nvs
  return nvs_erase_all ( nvshandle ) ;                // Clear all keys
}


//**************************************************************************************************
//                                      N V S G E T S T R                                          *
//**************************************************************************************************
// Read a string from nvs.                                                                         *
//**************************************************************************************************
String nvsgetstr ( const char* key )
{
  static char   nvs_buf[NVSBUFSIZE] ;       // Buffer for contents
  size_t        len = NVSBUFSIZE ;          // Max length of the string, later real length

  nvsopen() ;                               // Be sure to open nvs
  nvs_buf[0] = '\0' ;                       // Return empty string on error
  nvserr = nvs_get_str ( nvshandle, key, nvs_buf, &len ) ;
  if ( nvserr )
  {
    dbgprint ( "nvs_get_str failed %X for key %s, keylen is %d, len is %d!",
               nvserr, key, strlen ( key), len ) ;
    dbgprint ( "Contents: %s", nvs_buf ) ;
  }
  return String ( nvs_buf ) ;
}


//**************************************************************************************************
//                                      N V S S E T S T R                                          *
//**************************************************************************************************
// Put a key/value pair in nvs.  Length is limited to allow easy read-back.                        *
// No writing if no change.                                                                        *
//**************************************************************************************************
esp_err_t nvssetstr ( const char* key, String val )
{
  String curcont ;                                         // Current contents
  bool   wflag = true  ;                                   // Assume update or new key

  //dbgprint ( "Setstring for %s: %s", key, val.c_str() ) ;
  if ( val.length() >= NVSBUFSIZE )                        // Limit length of string to store
  {
    dbgprint ( "nvssetstr length failed!" ) ;
    return ESP_ERR_NVS_NOT_ENOUGH_SPACE ;
  }
  if ( nvssearch ( key ) )                                 // Already in nvs?
  {
    curcont = nvsgetstr ( key ) ;                          // Read current value
    wflag = ( curcont != val ) ;                           // Value change?
  }
  if ( wflag )                                             // Update or new?
  {
    //dbgprint ( "nvssetstr update value" ) ;
    nvserr = nvs_set_str ( nvshandle, key, val.c_str() ) ; // Store key and value
    if ( nvserr )                                          // Check error
    {
      dbgprint ( "nvssetstr failed!" ) ;
    }
  }
  return nvserr ;
}


//**************************************************************************************************
//                                      N V S C H K E Y                                            *
//**************************************************************************************************
// Change a keyname in in nvs.                                                                     *
//**************************************************************************************************
void nvschkey ( const char* oldk, const char* newk )
{
  String curcont ;                                         // Current contents

  if ( nvssearch ( oldk ) )                                // Old key in nvs?
  {
    curcont = nvsgetstr ( oldk ) ;                         // Read current value
    nvs_erase_key ( nvshandle, oldk ) ;                    // Remove key
    nvssetstr ( newk, curcont ) ;                          // Insert new
  }
}


//**************************************************************************************************
//                                      N V S S E A R C H                                          *
//**************************************************************************************************
// Check if key exists in nvs.                                                                     *
//**************************************************************************************************
bool nvssearch ( const char* key )
{
  size_t        len = NVSBUFSIZE ;                      // Length of the string

  nvsopen() ;                                           // Be sure to open nvs
  nvserr = nvs_get_str ( nvshandle, key, NULL, &len ) ; // Get length of contents
  return ( nvserr == ESP_OK ) ;                         // Return true if found
}


//**************************************************************************************************
//                                      C L A I M S P I                                            *
//**************************************************************************************************
// Claim the SPI bus.  Uses FreeRTOS semaphores.                                                   *
// If the semaphore cannot be claimed within the time-out period, the function continues without   *
// claiming the semaphore.  This is incorrect but allows debugging.                                *
//**************************************************************************************************
void claimSPI ( const char* p )
{
  const              TickType_t ctry = 10 ;                 // Time to wait for semaphore
  uint32_t           count = 0 ;                            // Wait time in ticks
  static const char* old_id = "none" ;                      // ID that holds the bus

  while ( xSemaphoreTake ( SPIsem, ctry ) != pdTRUE  )      // Claim SPI bus
  {
    if ( count++ > 25 )
    {
      dbgprint ( "SPI semaphore not taken within %d ticks by CPU %d,"
                 " id %s.  Claimed by %s",
                 count * ctry,
                 xPortGetCoreID(),
                 p, old_id ) ;
    }
    if ( count >= 100 )
    {
      return ;                                               // Continue without semaphore
    }
  }
  old_id = p ;                                               // Remember ID holding the semaphore
}


//**************************************************************************************************
//                                   R E L E A S E S P I                                           *
//**************************************************************************************************
// Free the the SPI bus.  Uses FreeRTOS semaphores.                                                *
//**************************************************************************************************
void releaseSPI()
{
  xSemaphoreGive ( SPIsem ) ;                            // Release SPI bus
}


//**************************************************************************************************
//                                      Q U E U E T O P T                                          *
//**************************************************************************************************
// Queue a special function for the play task.                                                     *
// These are high priority messages like stop or start.  So we make sure the message fits.         *
//**************************************************************************************************
void queueToPt ( qdata_type func )
{
  qdata_struct     specchunk ;                          // Special function to queue

  if ( uxQueueSpacesAvailable ( dataqueue ) == 0 )      // Is there space?
  {
    xQueueReceive ( dataqueue, &specchunk, 0 ) ;        // No, take out one element
  }
  specchunk.datatyp = func ;                            // Put function in datatyp
  xQueueSendToFront ( dataqueue, &specchunk, 200 ) ;    // Send to queue (First Out)
}


//**************************************************************************************************
//                                      T F T S E T                                                *
//**************************************************************************************************
// Request to display a segment on TFT.  Version for char* and String parameter.                   *
//**************************************************************************************************
void tftset ( uint16_t inx, const char *str )
{
  if ( inx < TFTSECS )                                  // Segment available on display
  {
    if ( str )                                          // String specified?
    {
      tftdata[inx].str = String ( str ) ;               // Yes, set string
    }
    tftdata[inx].update_req = true ;                    // and request flag
  }
}

void tftset ( uint16_t inx, String& str )
{
  if ( inx < TFTSECS )                                  // Segment available on display
  {
    tftdata[inx].str = str ;                            // Set string
    tftdata[inx].update_req = true ;                    // and request flag
  }
}


//**************************************************************************************************
//                                     G E T  P R E S E T  N A M E                                 *
//**************************************************************************************************
// Extract name from the preset string                                                             *
//**************************************************************************************************
 bool getPresetName (int16_t presetId, String &str) {
  bool defaultName = false;
  int16_t inx;

  str = readhostfrompref ( presetId ) ;                     // Get host spec and possible comment        
  if (str != "") {
    inx = str.indexOf ( "#" ) ;                             // Get position of "#"
    if ( inx > 0 ) {                                        // Hash sign present?
      if (str.charAt(inx+1) == '!') {
        inx += 1;
        defaultName = true;                                 // ! defualt name detected
      }
      str.remove ( 0, inx + 1 ) ;                           // Yes, remove non-comment part
    }
    chomp ( str ) ;                                         // Remove garbage from description
  }
  return defaultName;
}


#ifndef ETHERNET
//**************************************************************************************************
//                                        L I S T N E T W O R K S                                  *
//**************************************************************************************************
// List the available networks.                                                                    *
// Acceptable networks are those who have an entry in the preferences.                             *
// SSIDs of available networks will be saved for use in webinterface.                              *
//**************************************************************************************************
void listNetworks()
{
  WifiInfo_t       winfo ;            // Entry from wifilist
  wifi_auth_mode_t encryption ;       // TKIP(WPA), WEP, etc.
  const char*      acceptable ;       // Netwerk is acceptable for connection
  int              i, j ;             // Loop control

  dbgprint ( "Scan Networks" ) ;                         // Scan for nearby networks
  numSsid = WiFi.scanNetworks() ;
  dbgprint ( "Scan completed" ) ;
  networks = String ( "" ) ;
  if ( numSsid <= 0 )
  {
    dbgprint ( "Couldn't get a wifi connection" ) ;
    return ;
  }
  // print the list of networks seen:
  dbgprint ( "Number of available networks: %d",
             numSsid ) ;
  // Print the network number and name for each network found and
  for ( i = 0 ; i < numSsid ; i++ )
  {
    acceptable = "" ;                                    // Assume not acceptable
    for ( j = 0 ; j < wifilist.size() ; j++ )            // Search in wifilist
    {
      winfo = wifilist[j] ;                              // Get one entry
      if ( WiFi.SSID(i).indexOf ( winfo.ssid ) == 0 )    // Is this SSID acceptable?
      {
        acceptable = "Acceptable" ;
        break ;
      }
    }
    encryption = WiFi.encryptionType ( i ) ;
    dbgprint ( "%2d - %-25s Signal: %3d dBm, Encryption %4s, %s",
               i + 1, WiFi.SSID(i).c_str(), WiFi.RSSI(i),
               getEncryptionType ( encryption ),
               acceptable ) ;
    // Remember this network for later use
    networks += WiFi.SSID(i) + String ( "|" ) ;
  }
  dbgprint ( "End of list" ) ;
}
#endif


//**************************************************************************************************
//                                          U P D A T E N R                                        *
//**************************************************************************************************
// Used by nextPreset because update for preset and playlist number is about the same.             *
// Modify the pnr, handle over- and underflow. handle relative setting.                            *
//**************************************************************************************************
bool updateNr ( int16_t* pnr, int16_t maxnr, int16_t nr, bool relative )
{
  bool res = true ;                                           // Assume positive result

  dbgprint ( "updateNr %d <= %d to %d, relative is %d",
             *pnr, maxnr, nr, relative ) ;
  if ( relative )                                             // Relative to pnr?
  {
    *pnr += nr ;                                              // Yes, compute new pnr
  }
  else
  {
    *pnr = nr ;                                               // Not relative, set direct pnr
  }
  if ( *pnr < 0 )                                             // Check result
  {
    res = false ;                                             // Negative result, set bad result
    *pnr = maxnr ;                                            // and wrap
  }
  if ( *pnr > maxnr )                                         // Check if result beyond max
  {
    res = false ;                                             // Too high, set bad result
    *pnr = 0 ;                                                // and wrap
  }
  dbgprint ( "updateNr result is %d", *pnr ) ;
  return res ;                                                // Return the result
}


//**************************************************************************************************
//                                          N E X T P R E S E T                                    *
//**************************************************************************************************
// Set the preset for the next station.  May be relative.                                          *
//**************************************************************************************************
void nextPreset ( int16_t pnr, bool relative = false )
{
  //dbgprint ( "nextpreset called with pnr = %d", pnr ) ;
  if ( ( presetinfo.station_state == ST_STATION ) ||           // In station mode?
       ( presetinfo.station_state == ST_REDIRECT ) )           // or redirect mode?
  {
    presetinfo.station_state = ST_PRESET ;                     // No "next" in station/redirect mode
  }
  if ( presetinfo.station_state == ST_PLAYLIST )               // In playlist mode?
  {
    if ( ! updateNr ( &presetinfo.playlistnr,                  // Yes, next index possible?
                      presetinfo.highest_playlistnr,
                      pnr, relative ) )
    {
      presetinfo.station_state = ST_PRESET ;                   // No, end playlist mode
    }
  }
  if ( presetinfo.station_state == ST_PRESET )                 // In preset mode?
  {
    updateNr ( &presetinfo.preset,                             // Select next preset
               presetinfo.highest_preset,
               pnr, relative ) ;
    presetinfo.host = readhostfrompref ( presetinfo.preset ) ; // Set host
    dbgprint ( "nextPreset is %d",
               presetinfo.preset ) ;
  }
}


//**************************************************************************************************
//                                          T I M E R 1 0 S E C                                    *
//**************************************************************************************************
// Extra watchdog.  Called every 10 seconds.                                                       *
// If totalcount has not been changed, there is a problem and playing will stop.                   *
// Note that calling timely procedures within this routine or in called functions will             *
// cause a crash!                                                                                  *
//**************************************************************************************************
void IRAM_ATTR timer10sec()
{
  static uint32_t oldtotalcount = 7321 ;          // Needed for change detection
  static uint8_t  morethanonce = 0 ;              // Counter for succesive fails
  uint32_t        bytesplayed ;                   // Bytes send to MP3 converter

  if ( datamode & ( INIT | HEADER | DATA |        // Test op playing
                    METADATA | PLAYLISTINIT |
                    PLAYLISTHEADER |
                    PLAYLISTDATA ) )
  {
    bytesplayed = totalcount - oldtotalcount ;    // Nunber of bytes played in the 10 seconds
    oldtotalcount = totalcount ;                  // Save for comparison in next cycle
    if ( bytesplayed == 0 )                       // Still playing?
    {
      if ( morethanonce > 10 )                    // No! Happened too many times?
      {
        ESP.restart() ;                           // Reset the CPU, probably no return
      }
      //if ( datamode & ( PLAYLISTDATA |          // In playlist mode?
      //                  PLAYLISTINIT |
      //                  PLAYLISTHEADER ) )
      //{
      //  playlist_num = 0 ;                      // Yes, end of playlist
      //}
      //if ( ( morethanonce > 0 ) ||              // Happened more than once?
      //     ( playlist_num > 0 ) )               // Or playlist active?
      if ( morethanonce > 0 )                     // Happened more than once?
      {
        datamode = STOPREQD ;                     // Stop player
      }
      morethanonce++ ;                            // Count the fails
    }
    else
    {
      //                                          // Data has been send to MP3 decoder
      // Bitrate in kbits/s is bytesplayed / 10 / 1000 * 8
      mbitrate = ( bytesplayed + 625 ) / 1250 ;   // Measured bitrate
      morethanonce = 0 ;                          // Data seen, reset failcounter
    }
  }
}


//**************************************************************************************************
//                                          T I M E R 1 0 0                                        *
//**************************************************************************************************
// Called every 100 msec on interrupt level, so must be in IRAM and no lengthy operations          *
// allowed.                                                                                        *
//**************************************************************************************************
void IRAM_ATTR timer100()
{
  sv int16_t   count10sec = 0 ;                   // Counter for activatie 10 seconds process
  sv int16_t   eqcount = 0 ;                      // Counter for equal number of clicks
  sv int16_t   oldclickcount = 0 ;                // To detect difference

  spftrigger = true ;                             // Activate spfuncs
  if ( ++count10sec == 100  )                     // 10 seconds passed?
  {
    timer10sec() ;                                // Yes, do 10 second procedure
    count10sec = 0 ;                              // Reset count
  }
  if ( ( count10sec % 10 ) == 0 )                 // One second over?
  {
    if ( ++timeinfo.tm_sec >= 60 )                // Yes, update number of seconds
    {
      timeinfo.tm_sec = 0 ;                       // Wrap after 60 seconds
      if ( ++timeinfo.tm_min >= 60 )
      {
        timeinfo.tm_min = 0 ;                     // Wrap after 60 minutes
        if ( ++timeinfo.tm_hour >= 24 )
        {
          timeinfo.tm_hour = 0 ;                  // Wrap after 24 hours
        }
      }
    }
    time_req = true ;                             // Yes, show current time request
    if ( ++bltimer == BL_TIME )                   // Time to blank the TFT screen?
    {
      bltimer = 0 ;                               // Yes, reset counter
      blset ( false ) ;                           // Disable TFT (backlight)
    }
  }
  // Handle rotary encoder. Inactivity counter will be reset by encoder interrupt
  if ( enc_inactivity < 36000 )                   // Count inactivity time, but limit to 36000
  {
    enc_inactivity++ ;
  }
  // Now detection of single/double click of rotary encoder switch or ZIPPY B5
  if ( clickcount )                               // Any click?
  {
    if ( oldclickcount == clickcount )            // Yes, stable situation?
    {
      if ( ++eqcount == 6 )                       // Long time stable?
      {
        eqcount = 0 ;
        if ( clickcount > 2 )                     // Triple click?
        {
          tripleclick = true ;                    // Yes, set result
        }
        else if ( clickcount == 2 )               // Double click?
        {
          doubleclick = true ;                    // Yes, set result
        }
        else
        {
          singleclick = true ;                    // Just one click seen
        }
        clickcount = 0 ;                          // Reset number of clicks
      }
    }
    else
    {
      oldclickcount = clickcount ;                // To detect change
      eqcount = 0 ;                               // Not stable, reset count
    }
  }
}


//**************************************************************************************************
//                                          I S R _ I R                                            *
//**************************************************************************************************
// Interrupts received from VS1838B on every change of the signal.                                 *
// Intervals are 640 or 1640 microseconds for data.  syncpulses are 3400 micros or longer.         *
// Input is complete after 65 level changes.                                                       *
// Only the last 32 level changes are significant and will be handed over to common data.          *
//**************************************************************************************************
void IRAM_ATTR isr_IR()
{
  sv uint32_t      t0 = 0 ;                          // To get the interval
  sv uint32_t      ir_locvalue = 0 ;                 // IR code
  sv int           ir_loccount = 0 ;                 // Length of code
  uint32_t         t1, intval ;                      // Current time and interval since last change
  uint32_t         mask_in = 2 ;                     // Mask input for conversion
  uint16_t         mask_out = 1 ;                    // Mask output for conversion

  ir_intcount++ ;                                    // Test IR input.
  t1 = micros() ;                                    // Get current time
  intval = t1 - t0 ;                                 // Compute interval
  t0 = t1 ;                                          // Save for next compare
  if ( ( intval > 300 ) && ( intval < 800 ) )        // Short pulse?
  {
    ir_locvalue = ir_locvalue << 1 ;                 // Shift in a "zero" bit
    ir_loccount++ ;                                  // Count number of received bits
    ir_0 = ( ir_0 * 3 + intval ) / 4 ;               // Compute average durartion of a short pulse
  }
  else if ( ( intval > 1400 ) && ( intval < 1900 ) ) // Long pulse?
  {
    ir_locvalue = ( ir_locvalue << 1 ) + 1 ;         // Shift in a "one" bit
    ir_loccount++ ;                                  // Count number of received bits
    ir_1 = ( ir_1 * 3 + intval ) / 4 ;               // Compute average durartion of a short pulse
  }
  else if ( ir_loccount == 65 )                      // Value is correct after 65 level changes
  {
    while ( mask_in )                                // Convert 32 bits to 16 bits
    {
      if ( ir_locvalue & mask_in )                   // Bit set in pattern?
      {
        ir_value |= mask_out ;                       // Set set bit in result
      }
      mask_in <<= 2 ;                                // Shift input mask 2 positions
      mask_out <<= 1 ;                               // Shift output mask 1 position
    }
    ir_loccount = 0 ;                                // Ready for next input
  }
  else
  {
    ir_locvalue = 0 ;                                // Reset decoding
    ir_loccount = 0 ;
  }
}
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
void loop()
{
  if ( resetreq )                                   // Reset requested?
  {
    delay ( 1000 ) ;                                // Yes, wait some time
    ESP.restart() ;                                 // Reboot
  }
  scanserial() ;                                    // Handle serial input
  scanserial2() ;                                   // Handle serial input from NEXTION (if active)
  #ifdef SCANDIGITAL
  scandigital() ;                                   // Scan digital inputs
  #endif
  #ifdef SCANANALOG
  scananalog();
  #endif
  scanIR() ;                                        // See if IR input
  otaHandle() ;                                     // Check for OTA
  if ( mqtt_on )                                    // Need to handle MQTT?
  {
    mqttclient.loop() ;                             // Handling of MQTT connection
  }
  handleSaveReq() ;                                 // See if time to save settings
  handleIpPub() ;                                   // See if time to publish IP
  handleVolPub() ;                                  // See if time to publish volume
  chk_enc() ;                                       // Check rotary encoder functions
  radiofuncs() ;                                    // Handle start/stop commands for icecast
  spfuncs() ;                                       // Handle special functions
  sdfuncs() ;                                       // Do SD card related functions
  if ( testreq )
  {
    testreq = false ;
    // heap_caps_print_heap_info ( MALLOC_CAP_8BIT ) ;
    dbgprint ( "Stack maintask  is %d", uxTaskGetStackHighWaterMark ( maintask   ) ) ;
    dbgprint ( "Stack playtask  is %d", uxTaskGetStackHighWaterMark ( xplaytask  ) ) ;
    dbgprint ( "ADC reading is %d, filtered %d", adcvalraw, adcval ) ;
    dbgprint ( "%d IR interrupts seen", ir_intcount ) ;
  }
}


//**************************************************************************************************
//                             D E C O D E _ S P E C _ C H A R S                                   *
//**************************************************************************************************
// Decode special characters like "&#39;".                                                         *
//**************************************************************************************************
String decode_spec_chars ( String str )
{
  int    inx, inx2 ;                                // Indexes in string
  char   c ;                                        // Character from string
  char   val ;                                      // Converted character
  String res = str ;

  while ( ( inx = res.indexOf ( "&#" ) ) >= 0 )     // Start sequence in string?
  {
    inx2 = res.indexOf ( ";", inx ) ;               // Yes, search for stop character
    if ( inx2 < 0 )                                 // Stop character found
    {
      break ;                                       // Malformed string
    }
    res = str.substring ( 0, inx ) ;                // First part
    inx += 2 ;                                      // skip over start sequence
    val = 0 ;                                       // Init result of 
    while ( ( c = str[inx++] ) != ';' )             // Convert character
    {
      val = val * 10 + c - '0' ;
    }
    res += ( String ( val ) +                       // Add special char to string
             str.substring ( ++inx2 ) ) ;           // Add rest of string
  }
  return res ;
}


//**************************************************************************************************
//                                    C H K H D R L I N E                                          *
//**************************************************************************************************
// Check if a line in the header is a reasonable headerline.                                       *
// Normally it should contain something like "icy-xxxx:abcdef".                                    *
//**************************************************************************************************
bool chkhdrline ( const char* str )
{
  char    b ;                                         // Byte examined
  int     len = 0 ;                                   // Lengte van de string

  while ( ( b = *str++ ) )                            // Search to end of string
  {
    len++ ;                                           // Update string length
    if ( ! isalpha ( b ) )                            // Alpha (a-z, A-Z)
    {
      if ( b != '-' )                                 // Minus sign is allowed
      {
        if ( b == ':' )                               // Found a colon?
        {
          return ( ( len > 5 ) && ( len < 70 ) ) ;    // Yes, okay if length is okay
        }
        else
        {
          return false ;                              // Not a legal character
        }
      }
    }
  }
  return false ;                                      // End of string without colon
}


//**************************************************************************************************
//                            S C A N _ C O N T E N T _ L E N G T H                                *
//**************************************************************************************************
// If the line contains content-length information: set clength (content length counter).          *
//**************************************************************************************************
void scan_content_length ( const char* metalinebf )
{
  if ( strstr ( metalinebf, "Content-Length" ) )        // Line contains content length
  {
    clength = atoi ( metalinebf + 15 ) ;                // Yes, set clength
    dbgprint ( "Content-Length is %d", clength ) ;      // Show for debugging purposes
  }
}


//**************************************************************************************************
//                                   H A N D L E B Y T E _ C H                                     *
//**************************************************************************************************
// Handle the next byte of data from server.                                                       *
// Chunked transfer encoding aware. Chunk extensions are not supported.                            *
//**************************************************************************************************
void handlebyte_ch ( uint8_t b )
{
  static int       chunksize = 0 ;                      // Chunkcount read from stream
  static uint16_t  playlistcnt ;                        // Counter to find right entry in playlist
  static int       LFcount ;                            // Detection of end of header
  static bool      ctseen = false ;                     // First line of header seen or not
  static bool      redirection = false ;                // Redirection or not
  String tmp="";

  if ( chunked &&
       ( datamode & ( DATA |                           // Test op DATA handling
                      METADATA |
                      PLAYLISTDATA ) ) )
  {
    if ( chunkcount == 0 )                             // Expecting a new chunkcount?
    {
      if ( b == '\r' )                                 // Skip CR
      {
        return ;
      }
      else if ( b == '\n' )                            // LF ?
      {
        chunkcount = chunksize ;                       // Yes, set new count
        chunksize = 0 ;                                // For next decode
        return ;
      }
      // We have received a hexadecimal character.  Decode it and add to the result.
      b = toupper ( b ) - '0' ;                        // Be sure we have uppercase
      if ( b > 9 )
      {
        b = b - 7 ;                                    // Translate A..F to 10..15
      }
      chunksize = ( chunksize << 4 ) + b ;
      return  ;
    }
    chunkcount-- ;                                     // Update count to next chunksize block
  }
  if ( datamode == DATA )                              // Handle next byte of MP3/AAC/Ogg data
  {
    *outqp++ = b ;
    if ( outqp == ( outchunk.buf + sizeof(outchunk.buf) ) ) // Buffer full?
    {
      // Send data to playtask queue.  If the buffer cannot be placed within 200 ticks,
      // the queue is full, while the sender tries to send more.  The chunk will be dis-
      // carded it that case.
      xQueueSend ( dataqueue, &outchunk, 200 ) ;       // Send to queue
      outqp = outchunk.buf ;                           // Item empty now
    }
    if ( metaint )                                     // No METADATA on Ogg streams or mp3 files
    {
      if ( --datacount == 0 )                          // End of datablock?
      {
        setdatamode ( METADATA ) ;
        metalinebfx = -1 ;                             // Expecting first metabyte (counter)
      }
    }
    return ;
  }
  if ( datamode == INIT )                              // Initialize for header receive
  {
    ctseen = false ;                                   // Contents type not seen yet
    redirection = false ;                              // No redirection found yet
    outqp = outchunk.buf ;                             // Item empty now
    metaint = 0 ;                                      // No metaint found
    LFcount = 0 ;                                      // For detection end of header
    bitrate = 0 ;                                      // Bitrate still unknown
    dbgprint ( "Switch to HEADER" ) ;
    setdatamode ( HEADER ) ;                           // Handle header
    totalcount = 0 ;                                   // Reset totalcount
    metalinebfx = 0 ;                                  // No metadata yet
    metalinebf[0] = '\0' ;
  }
  if ( datamode == HEADER )                            // Handle next byte of MP3 header
  {
    if ( ( b > 0x7F ) ||                               // Ignore unprintable characters
         ( b == '\r' ) ||                              // Ignore CR
         ( b == '\0' ) )                               // Ignore NULL
    {
      // Yes, ignore
    }
    else if ( b == '\n' )                              // Linefeed ?
    {
      LFcount++ ;                                      // Count linefeeds
      metalinebf[metalinebfx] = '\0' ;                 // Take care of delimiter
      if ( chkhdrline ( metalinebf ) )                 // Reasonable input?
      {
        dbgprint ( "Headerline: %s",                   // Show headerline
                   metalinebf ) ;
        String metaline = String ( metalinebf ) ;      // Convert to string
        String lcml = metaline ;                       // Use lower case for compare
        lcml.toLowerCase() ;
        if ( lcml.startsWith ( "location: " ) )        // Redirection?
        {
          metaline = metaline.substring ( 10 ) ;       // Yes, get new URL
          int hp = metaline.indexOf ( "://" ) ;        // Redirection with "http(s)://" ?
          if ( hp > 0 )
          {
            metaline = metaline.substring ( hp + 3 ) ; // Yes, get new URL
          }
          presetinfo.station_state = ST_REDIRECT ;     // Set host already filled
          presetinfo.host= metaline ;
          redirection = true ;                         // Remember redirection
        }
        if ( lcml.startsWith ( "content-type" ) )      // Line with "Content-Type: xxxx/yyy"
        {
          ctseen = true ;                              // Yes, remember seeing this
          audio_ct = metaline.substring ( 13 ) ;       // Set contentstype
          audio_ct.trim() ;
          //dbgprint ( "%s seen", audio_ct.c_str() ) ; // Like "audio/mpeg"
        }
        if ( lcml.startsWith ( "icy-br:" ) )
        {
          bitrate = metaline.substring(7).toInt() ;    // Found bitrate tag, read the bitrate
          if ( bitrate == 0 )                          // For Ogg br is like "Quality 2"
          {
            bitrate = 87 ;                             // Dummy bitrate
          }
        }
        else if ( lcml.startsWith ("icy-metaint:" ) )
        {
          metaint = metaline.substring(12).toInt() ;   // Found metaint tag, read the value
        }
        else if ( lcml.startsWith ( "icy-name:" ) )
        {
          icyname = metaline.substring(9) ;            // Get station name
          icyname = decode_spec_chars ( icyname ) ;    // Decode special characters in name
          icyname.trim() ;                             // Remove leading and trailing spaces

          // tftset ( 2, icyname ) ;                      // Set screen segment bottom part
          tftset ( 2,  getPresetName(presetinfo.preset, tmp)?tmp:icyname) ;
          mqttpub.trigger ( MQTT_ICYNAME ) ;           // Request publishing to MQTT
        }
        else if ( lcml.startsWith ( "transfer-encoding:" ) )
        {
          // Station provides chunked transfer
          if ( lcml.endsWith ( "chunked" ) )
          {
            chunked = true ;                           // Remember chunked transfer mode
            chunkcount = 0 ;                           // Expect chunkcount in DATA
          }
        }
      }
      metalinebfx = 0 ;                                // Reset this line
      if ( LFcount == 2 )                              // Double LF marks end of header?
      {
        if ( redirection )                             // Redirection?
        {
          dbgprint ( "Redirect" ) ;                    // Yes, show
          setdatamode ( INIT ) ;                       // Mode to INIT again
          myQueueSend ( radioqueue, &startcmd ) ;      // Restart with new found host
        }
        else if ( ctseen )                             // Content type seen?
        {
          dbgprint ( "Switch to DATA, bitrate is %d"   // Show bitrate
                    ", metaint is %d",                 // and metaint
                    bitrate, metaint ) ;
          setdatamode ( DATA ) ;                       // Expecting data now
          datacount = metaint ;                        // Number of bytes before first metadata
          queueToPt ( QSTARTSONG ) ;                   // Queue a request to start song
        }
      }
    }
    else
    {
      metalinebf[metalinebfx++] = (char)b ;            // Normal character, put new char in metaline
      if ( metalinebfx >= METASIZ )                    // Prevent overflow
      {
        metalinebfx-- ;
      }
      LFcount = 0 ;                                    // Reset double CRLF detection
    }
    return ;
  }
  if ( datamode == METADATA )                          // Handle next byte of metadata
  {
    if ( metalinebfx < 0 )                             // First byte of metadata?
    {
      metalinebfx = 0 ;                                // Prepare to store first character
      metacount = b * 16 + 1 ;                         // New count for metadata including length byte
    }
    else
    {
      metalinebf[metalinebfx++] = (char)b ;            // Normal character, put new char in metaline
      if ( metalinebfx >= METASIZ )                    // Prevent overflow
      {
        metalinebfx-- ;
      }
    }
    if ( --metacount == 0 )
    {
      metalinebf[metalinebfx] = '\0' ;                 // Make sure line is limited
      if ( strlen ( metalinebf ) )                     // Any info present?
      {
        // metaline contains artist and song name.  For example:
        // "StreamTitle='Don McLean - American Pie';StreamUrl='';"
        // Sometimes it is just other info like:
        // "StreamTitle='60s 03 05 Magic60s';StreamUrl='';"
        // Isolate the StreamTitle, remove leading and trailing quotes if present.
        showstreamtitle ( metalinebf ) ;               // Show artist and title if present in metadata
        mqttpub.trigger ( MQTT_STREAMTITLE ) ;         // Request publishing to MQTT
      }
      if ( metalinebfx  > ( METASIZ - 10 ) )           // Unlikely metaline length?
      {
        dbgprint ( "Metadata block too long!" ) ;      // Probably no metadata
        // Skipping all Metadata from now on.
        metaint = 0 ;
      }
      datacount = metaint ;                            // Reset data count
      //bufcnt = 0 ;                                   // Reset buffer count
      setdatamode ( DATA ) ;                           // Expecting data
    }
  }
  if ( datamode == PLAYLISTINIT )                      // Initialize for receive .m3u file
  {
    // We are going to use metadata to read the lines from the .m3u file
    // Sometimes this will only contain a single line
    metalinebfx = 0 ;                                  // Prepare for new line
    LFcount = 0 ;                                      // For detection end of header
    setdatamode ( PLAYLISTHEADER ) ;                   // Handle playlist header
    playlistcnt = 0 ;                                  // Reset for compare
    totalcount = 0 ;                                   // Reset totalcount
    clength = 0xFFFFFFFF ;                             // Content-length unknown
    dbgprint ( "Read from playlist" ) ;
  }
  if ( datamode == PLAYLISTHEADER )                    // Read header
  {
    if ( ( b > 0x7F ) ||                               // Ignore unprintable characters
         ( b == '\r' ) ||                              // Ignore CR
         ( b == '\0' ) )                               // Ignore NULL
    {
      return ;                                         // Quick return
    }
    else if ( b == '\n' )                              // Linefeed ?
    {
      LFcount++ ;                                      // Count linefeeds
      metalinebf[metalinebfx] = '\0' ;                 // Take care of delimeter
      dbgprint ( "Playlistheader: %s",                 // Show playlistheader
                 metalinebf ) ;
      scan_content_length ( metalinebf ) ;             // Check if it is a content-length line
      metalinebfx = 0 ;                                // Ready for next line
      if ( LFcount == 2 )
      {
        dbgprint ( "Switch to PLAYLISTDATA, "          // For debug
                   "search for entry %d",
                   presetinfo.playlistnr ) ;
        setdatamode ( PLAYLISTDATA ) ;                 // Expecting data now
        mqttpub.trigger ( MQTT_PLAYLISTPOS ) ;         // Playlistposition to MQTT
        return ;
      }
    }
    else
    {
      metalinebf[metalinebfx++] = (char)b ;            // Normal character, put new char in metaline
      if ( metalinebfx >= METASIZ )                    // Prevent overflow
      {
        metalinebfx-- ;
      }
      LFcount = 0 ;                                    // Reset double CRLF detection
    }
  }
  if ( datamode == PLAYLISTDATA )                      // Read next byte of .m3u file data
  {
    clength-- ;                                        // Decrease content length by 1
    if ( ( b > 0x7F ) ||                               // Ignore unprintable characters
         ( b == '\r' ) ||                              // Ignore CR
         ( b == '\0' ) )                               // Ignore NULL
    {
      // Yes, ignore
    }
    if ( b != '\n' )                                   // Linefeed?
    { // No, normal character in playlistdata,
      metalinebf[metalinebfx++] = (char)b ;            // add it to metaline
      if ( metalinebfx >= METASIZ )                    // Prevent overflow
      {
        metalinebfx-- ;
      }
    }
    if ( ( b == '\n' ) ||                              // linefeed?
         ( clength == 0 ) )                            // Or end of playlist data contents
    {
      int inx ;                                        // Pointer in metaline
      metalinebf[metalinebfx] = '\0' ;                 // Take care of delimeter
      dbgprint ( "Playlistdata: %s",                   // Show playlist data
                 metalinebf ) ;
      if ( strlen ( metalinebf ) < 5 )                 // Skip short lines
      {
        metalinebfx = 0 ;                              // Flush line
        metalinebf[0] = '\0' ;
        return ;
      }
      String metaline = String ( metalinebf ) ;        // Convert to string
      if ( metaline.indexOf ( "#EXTINF:" ) >= 0 )      // Info?
      {
        if ( presetinfo.playlistnr == playlistcnt )    // Info for this entry?
        {
          inx = metaline.indexOf ( "," ) ;             // Comma in this line?
          if ( inx > 0 )
          {
            // Show artist and title if present in metadata
            showstreamtitle ( metaline.substring ( inx + 1 ).c_str(), true ) ;
            mqttpub.trigger ( MQTT_STREAMTITLE ) ;     // Request publishing to MQTT
          }
        }
      }
      if ( metaline.startsWith ( "#" ) )               // Commentline?
      {
        metalinebfx = 0 ;                              // Yes, ignore
        return ;                                       // Ignore commentlines
      }
      // Now we have an URL for a .mp3 file or stream.
      presetinfo.highest_playlistnr = playlistcnt ;
      dbgprint ( "Entry %d in playlist found: %s", playlistcnt, metalinebf ) ;
      if ( presetinfo.playlistnr == playlistcnt )      // Is it the right one?
      {
        inx = metaline.indexOf ( "://" ) ;             // Search for "http(s)://"
        if ( inx >= 0 )                                // Does URL contain "http://"?
        {
          metaline = metaline.substring ( inx + 3 ) ;  // Yes, remove it
        }
        presetinfo.host = metaline ;                   // Set host
        presetinfo.station_state = ST_PLAYLIST ;       // Set playlist mode
        setdatamode ( INIT ) ;                         // Yes, mode to INIT again
        myQueueSend ( radioqueue, &startcmd ) ;        // Restart with new found host
      }
      metalinebfx = 0 ;                                // Prepare for next line
      playlistcnt++ ;                                  // Next entry in playlist
    }
  }
}


//**************************************************************************************************
//                                  H A N D L E _ N O T F O U N D                                  *
//**************************************************************************************************
// If parameters are present: handle them.                                                         *
// Otherwise: transfer file from SPIFFS to webserver client.                                       *
//**************************************************************************************************
void handle_notfound ( AsyncWebServerRequest *request )
{
  String       ct = String ( "text/plain" ) ;         // Default content type
  String       path ;                                 // Filename for SPIFFS
  String       reply ;                                // Reply on not file request
  const char*  p ;                                    // Reply from analyzecmd
  int          numargs ;                              // Number of arguments
  int          i ;                                    // Index in arguments
  String       key ;                                  // Name of parameter i
  String       contents ;                             // Value of parameter i
  String       cmd ;                                  // Command to analyze
  String       sndstr = String() ;                    // String to send

  numargs = request->params() ;                       // Haal aantal parameters
  for ( i = 0 ; i < numargs ; i++ )                   // Scan de parameters
  {
    key = request->argName ( i ) ;                    // Get name (key)
    contents = request->arg ( i ) ;                   // Get value
    chomp ( key ) ;                                   // Remove leading/trailing spaces
    chomp ( contents ) ;                              // Remove leading/trailing spaces
    if ( key == "version" )                           // Skip "version" parameter
    {
      continue ;
    }
    cmd = key + String ( "=" ) + contents ;           // Format command to analyze
    p = analyzeCmd ( cmd.c_str() ) ;                  // Analyze command
    sndstr += String ( p ) ;                          // Content of HTTP response follows the header
  }
  if ( ! sndstr.isEmpty() )                           // Any argument handled?
  {
    request->send ( 200, ct, sndstr ) ;               // Send reply
    return ;                                          // Quick return
  }
  // No parameters, it is just a request for a new page, style sheet or icon
  path = request->url() ;                             // Path for requested filename
  if ( path == String ( "/" ) )                       // Default is index.html
  {
    path = String ( "/index.html" ) ;                 // Select index.html
  }
  #ifndef SDCARD
    if ( path == "/mp3play.html" )                    // MP3 player page requested?
    {
      path = "/nomp3play.html" ;                      // Yes, select dummy mp3 player page
    }
  #endif
  if ( SPIFFS.exists ( path ) )                       // Does it exist in SPIFFS?
  {
    ct = getContentType ( path ) ;                    // Get content type
    request->send ( SPIFFS, path, ct ) ;              // Send to client
  }
  else
  {
    request->send ( 200, ct, String ( "sorry" ) ) ;   // Send reply
  }
}




//**************************************************************************************************
//                                         C H O M P                                               *
//**************************************************************************************************
// Do some filtering on de inputstring:                                                            *
//  - String comment part (starting with "#").                                                     *
//  - Strip trailing CR.                                                                           *
//  - Strip leading spaces.                                                                        *
//  - Strip trailing spaces.                                                                       *
//**************************************************************************************************
void chomp ( String &str ) { 
  int  inx ;                                         // Index in de input string

  if ( ( inx = str.indexOf ( "#" ) ) >= 0 ) {        // Comment line or partial comment?
    str.remove ( inx ) ;                             // Yes, remove
  }
  str.trim() ;                                        // Remove spaces and CR
}


//**************************************************************************************************
//                                     A N A L Y Z E C M D                                         *
//**************************************************************************************************
// Handling of the various commands from remote webclient, Serial or MQTT.                         *
// Version for handling string with: <parameter>=<value>                                           *
//**************************************************************************************************
const char* analyzeCmd ( const char* str )
{
  char*        value ;                           // Points to value after equalsign in command
  const char*  res ;                             // Result of analyzeCmd

  value = strstr ( str, "=" ) ;                  // See if command contains a "="
  if ( value )
  {
    *value = '\0' ;                              // Separate command from value
    res = analyzeCmd ( str, value + 1 ) ;        // Analyze command and handle it
    *value = '=' ;                               // Restore equal sign
  }
  else
  {
    res = analyzeCmd ( str, "0" ) ;              // No value, assume zero
  }
  return res ;
}


//**************************************************************************************************
//                                     A N A L Y Z E C M D                                         *
//**************************************************************************************************
// Handling of the various commands from remote webclient, serial or MQTT.                         *
// par holds the parametername and val holds the value.                                            *
// "wifi_00" and "preset_00" may appear more than once, like wifi_01, wifi_02, etc.                *
// Examples with available parameters:                                                             *
//   preset     = 12                        // Select start preset to connect to                   *
//   track      = 34                        // Select MP3 track from SD card                       *
//   preset_00  = <mp3 stream>              // Specify station for a preset 00-max *)              *
//   volume     = 95                        // Percentage between 0 and 100                        *
//   upvolume   = 2                         // Add percentage to current volume                    *
//   downvolume = 2                         // Subtract percentage from current volume             *
//   toneha     = <0..15>                   // Setting treble gain                                 *
//   tonehf     = <0..15>                   // Setting treble frequency                            *
//   tonela     = <0..15>                   // Setting bass gain                                   *
//   tonelf     = <0..15>                   // Setting treble frequency                            *
//   station    = <mp3 stream>              // Select new station (will not be saved)              *
//   station    = <URL>.mp3                 // Play standalone .mp3 file (not saved)               *
//   station    = <URL>.m3u                 // Select playlist (will not be saved)                 *
//   stop                                   // Stop playing                                        *
//   resume                                 // Resume playing                                      *
//   mute                                   // Mute/unmute the music (toggle)                      *
//   wifi_00    = mySSID/mypassword         // Set WiFi SSID and password *)                       *
//   mqttbroker = mybroker.com              // Set MQTT broker to use *)                           *
//   mqttprefix = XP93g                     // Set MQTT broker to use                              *
//   mqttport   = 1883                      // Set MQTT port to use, default 1883 *)               *
//   mqttuser   = myuser                    // Set MQTT user for authentication *)                 *
//   mqttpasswd = mypassword                // Set MQTT password for authentication *)             *
//   clk_server = pool.ntp.org              // Time server to be used *)                           *
//   clk_offset = <-11..+14>                // Offset with respect to UTC in hours *)              *
//   clk_dst    = <1..2>                    // Offset during daylight saving time in hours *)      *
//   settings                               // Returns setting like presets and tone               *
//   status                                 // Show current URL to play                            *
//   mp3list                                // Returns list with all MP3 files                     *
//   test                                   // For test purposes                                   *
//   debug      = 0 or 1                    // Switch debugging on or off                          *
//   reset                                  // Restart the ESP32                                   *
//   bat0       = 2318                      // ADC value for an empty battery                      *
//   bat100     = 2916                      // ADC value for a fully charged battery               *
//   Philips Fidelo new commands                                                                   *
//   toggle                                 // off/on player                                       *
//   bleds                                  // rotate brightness of bottom leds                    *
//  Commands marked with "*)" are sensible during initialization only                              *
//**************************************************************************************************
const char* analyzeCmd ( const char* par, const char* val )
{
  String             argument ;                       // Argument as string
  String             value ;                          // Value of an argument as a string
  String             tmpstr ;                         // Temporary storage of a string
  int                ivalue ;                         // Value of argument as an integer
  static char        reply[180] ;                     // Reply to client, will be returned
  bool               relative = false ;               // Relative argument (+ or -)

  blset ( true ) ;                                    // Enable backlight of TFT
  strcpy ( reply, "Command accepted" ) ;              // Default reply
  argument = String ( par ) ;                         // Get the argument
  chomp ( argument ) ;                                // Remove comment and useless spaces
  if ( argument.length() == 0 )                       // Lege commandline (comment)?
  {
    return reply ;                                    // Ignore
  }
  argument.toLowerCase() ;                            // Force to lower case
  value = String ( val ) ;                            // Get the specified value
  chomp ( value ) ;                                   // Remove comment and extra spaces
  ivalue = value.toInt() ;                            // Also as an integer
  if ( ( relative = argument.startsWith ( "up" ) ) )  // + relative setting?
  {
    argument = argument.substring ( 2 ) ;             // Remove the "up"-part
  }
  else if ( ( relative = 
                 argument.startsWith ( "down" )  ) )  // - relative setting?
  {
    ivalue = -ivalue ;                                // But with negative value
    argument = argument.substring ( 4 ) ;             // Remove the "down"-part
  }
  if ( value.startsWith ( "http://" ) )               // Does (possible) URL contain "http://"?
  {
    value.remove ( 0, 7 ) ;                           // Yes, remove it
  }
  if ( argument == "ota" )                            // Enable/disable OTA?
  {
    ota = ( ivalue != 0 ) ;                           // Yes, set switch acoordingly
  }
  else if ( argument == "volume" )                    // Volume setting?
  {
    // Volume may be of the form "upvolume", "downvolume" or "volume" for relative or absolute setting
    if ( relative )                                   // + relative setting?
    {
      ini_block.reqvol = player_getVolume() +         // Up/down by 0.5 or more dB
                         ivalue ;
    }
    else
    {
      ini_block.reqvol = ivalue ;                     // Absolue setting
    }
    if ( ini_block.reqvol > 127 )                     // Wrapped around?
    {
      ini_block.reqvol = 0 ;                          // Yes, keep at zero
    }
    if ( ini_block.reqvol > 100 )
    {
      ini_block.reqvol = 100 ;                        // Limit to normal values
    }
    muteflag = false ;                                // Stop possibly muting
    sprintf ( reply, "Volume is now %d",              // Reply new volume
              ini_block.reqvol ) ;
  }
  else if ( argument == "mute" )                      // Mute/unmute request
  {
    muteflag = !muteflag ;                            // Request volume to zero/normal
  }
  else if ( argument.startsWith ( "ir_" ) )           // Ir setting?
  { // Do not handle here
  }
  else if ( argument.startsWith ( "preset_" ) )       // Enumerated preset?
  {
    ivalue = argument.substring ( 7 ).toInt() ;       // Only look for max
  }
  else if ( argument == "preset" )                    // (UP/DOWN)Preset station?
  {
    nextPreset ( ivalue, relative ) ;                 // Yes, set new preset
    sprintf ( reply, "Preset is now %d",              // Reply new preset
              presetinfo.preset ) ;
    if ( NetworkFound )
      myQueueSend ( radioqueue, &startcmd ) ;           // Signal radiofuncs()
  }
#ifdef SDCARD
  else if ( argument == "track" )                     // MP3 track request?
  {
    if ( relative )                                   // Was it relative?
    {
      ivalue = getCurrentSDTrackNumber() + ivalue ;   // Yes, relative to current tracknumber
    }
    getSDFileName ( ivalue ) ;                        // Yes, select new track
    myQueueSend ( sdqueue, &startcmd ) ;              // Signal SDfuncs()
  }
#endif
  else if ( ( value.length() > 0 ) &&
            ( argument == "station" ) )               // Station in the form address:port
  {
    presetinfo.host = value ;                         // Save it for storage and selection later
    presetinfo.station_state = ST_STATION ;           // Set station mode
    myQueueSend ( radioqueue, &startcmd ) ;           // Signal radiofuncs()
    sprintf ( reply,
              "Select %s",                            // Format reply
              value.c_str() ) ;
    utf8ascii_ip ( reply ) ;                          // Remove possible strange characters
  }
  else if ( argument == "status" )                    // Status request
  {
    if ( datamode == STOPPED )
    {
      sprintf ( reply, "Player stopped" ) ;           // Format reply
    }
    else
    {
      sprintf ( reply, "%s - %s", icyname.c_str(),
                icystreamtitle.c_str() ) ;            // Streamtitle from metadata
    }
  }
  else if ( argument == "reset" )                     // Reset request
  {
    resetreq = true ;                                 // Reset all
  }
  else if ( argument == "test" )                      // Test command
  {
    sprintf ( reply, "Free memory is %d, chunks in queue %d, bitrate %d kbps",
              heapspace,
              uxQueueMessagesWaiting ( dataqueue ),
              mbitrate ) ;
    testreq = true ;                                  // Request to print info in main program
  }
  // Commands for bass/treble control
  else if ( argument.startsWith ( "tone" ) )          // Tone command
  {
    if ( argument.indexOf ( "ha" ) > 0 )              // High amplitue? (for treble)
    {
      ini_block.rtone[0] = ivalue ;                   // Yes, prepare to set ST_AMPLITUDE
    }
    if ( argument.indexOf ( "hf" ) > 0 )              // High frequency? (for treble)
    {
      ini_block.rtone[1] = ivalue ;                   // Yes, prepare to set ST_FREQLIMIT
    }
    if ( argument.indexOf ( "la" ) > 0 )              // Low amplitue? (for bass)
    {
      ini_block.rtone[2] = ivalue ;                   // Yes, prepare to set SB_AMPLITUDE
    }
    if ( argument.indexOf ( "lf" ) > 0 )              // High frequency? (for bass)
    {
      ini_block.rtone[3] = ivalue ;                   // Yes, prepare to set SB_FREQLIMIT
    }
    reqtone = true ;                                  // Set change request
    sprintf ( reply, "Parameter for bass/treble %s set to %d",
              argument.c_str(), ivalue ) ;
  }
  else if ( argument == "rate" )                      // Rate command?
  {
    player_AdjustRate ( ivalue ) ;                    // Yes, adjust
  }
  else if ( argument.startsWith ( "mqtt" ) )          // Parameter fo MQTT?
  {
    strcpy ( reply, "MQTT broker parameter changed. Save and restart to have effect" ) ;
    if ( argument.indexOf ( "broker" ) > 0 )          // Broker specified?
    {
      ini_block.mqttbroker = value ;                  // Yes, set broker accordingly
    }
    else if ( argument.indexOf ( "prefix" ) > 0 )     // Port specified?
    {
      ini_block.mqttprefix = value ;                  // Yes, set port user accordingly
    }
    else if ( argument.indexOf ( "port" ) > 0 )       // Port specified?
    {
      ini_block.mqttport = ivalue ;                   // Yes, set port user accordingly
    }
    else if ( argument.indexOf ( "user" ) > 0 )       // User specified?
    {
      ini_block.mqttuser = value ;                    // Yes, set user accordingly
    }
    else if ( argument.indexOf ( "passwd" ) > 0 )     // Password specified?
    {
      ini_block.mqttpasswd = value.c_str() ;          // Yes, set broker password accordingly
    }
  }
  else if ( argument == "debug" )                     // Debug on/off request?
  {
    dbg_set ( ivalue != 0 ) ;                         // Yes, set flag accordingly
  }
  else if ( argument == "getnetworks" )               // List all WiFi networks?
  {
    sprintf ( reply, networks.c_str() ) ;             // Reply is SSIDs
  }
  else if ( argument.startsWith ( "clk_" ) )          // TOD parameter?
  {
    if ( argument.indexOf ( "server" ) > 0 )          // Yes, NTP server spec?
    {
      ini_block.clk_server = value ;                  // Yes, set server
    }
    if ( argument.indexOf ( "offset" ) > 0 )          // Offset with respect to UTC spec?
    {
      ini_block.clk_offset = value.toInt() ;          // Yes, set offset
    }
    if ( argument.indexOf ( "dst" ) > 0 )             // Offset duringe DST spec?
    {
      ini_block.clk_dst = value.toInt() ;             // Yes, set DST offset
    }
  }
  else if ( argument.startsWith ( "bat" ) )           // Battery ADC value?
  {
    if ( argument.indexOf ( "100" ) == 3 )            // 100 percent value?
    {
      ini_block.bat100 = ivalue ;                     // Yes, set it
    }
    else if ( argument.indexOf ( "0" ) == 3 )         // 0 percent value?
    {
      ini_block.bat0 = ivalue ;                       // Yes, set it
    }
  }
  else if ( argument == "toggle" ) {                  // PvF: new command toggle radio status on/off
    if ( datamode == STOPPED ) {                      // if already stopped, start it
      if ( NetworkFound ) {                           // Start with preset if network available
        // nextPreset ( presetinfo.preset, false  ) ; // Resore last preset
        myQueueSend ( radioqueue, &startcmd ) ;       // Start player in radio mode
        sprintf ( reply, "Starting player" );
        dbgprint ( "Starting player %d", presetinfo.preset);
        String tmp = "";
        tftset ( 2,  getPresetName(presetinfo.preset, tmp)?tmp:icyname) ;
      }
    } else {                                          // ok, not stopped, then stop it
      myQueueSend ( sdqueue, &stopcmd );              // Stop player
      myQueueSend ( radioqueue, &stopcmd );           // Stop player
      setdatamode(STOPPED);                           // PfV: there is no data more
      displayStop();                                  // PfV: Update info on display
    }
  }  
  else if ( argument == "bleds" ) {                  // PvF: new command toggle radio status on/off
    PWMidx = setPWM(PWMidx,1);
  }  
  else
  {
    sprintf ( reply, "%s called with illegal parameter: %s",
              NAME, argument.c_str() ) ;
  }
  return reply ;                                      // Return reply to the caller
}

//**************************************************************************************************
//                                      D I S P L A Y STOP                                         *
//**************************************************************************************************
// Update info on display(s) on stopped player                                                      *
//**************************************************************************************************
void displayStop()
{

    tftset ( 1, "" );                                         // PfV: Update info on display
    tftset ( 2, "" );                                         // PfV: clear screen
    tftset ( 3, "Player OFF" ) ;                              // PvF: Player off on display
    #ifdef FIDELO
      fideDisplay.alarm(true);                                // PvF: in Stop mode turn on alarm LED
    #endif
}

//**************************************************************************************************
//* Function that are called from spfunc().                                                        *
//* Note that some device dependent function are place in the *.h files.                           *
//**************************************************************************************************

//**************************************************************************************************
//                                      D I S P L A Y I N F O                                      *
//**************************************************************************************************
// Show a string on the LCD at a specified y-position (0..2) in a specified color.                 *
// The parameter is the index in tftdata[].                                                        *
//**************************************************************************************************
void displayinfo ( uint16_t inx )
{
  uint16_t       width = dsp_getwidth() ;                  // Normal number of colums
  scrseg_struct* p = &tftdata[inx] ;
  uint16_t len ;                                           // Length of string, later buffer length

  if ( inx == 0 )                                          // Topline is shorter
  {
    width += TIMEPOS ;                                     // Leave space for time
  }
  if ( dsp_ok )                                            // TFT active?
  {
    dsp_fillRect ( 0, p->y, width, p->height, BLACK ) ;    // Clear the space for new info
    if ( ( dsp_getheight() > 64 ) && ( p->y > 1 ) )        // Need and space for divider?
    {
      dsp_fillRect ( 0, p->y - 4, width, 1, GREEN ) ;      // Yes, show divider above text
    }
    len = p->str.length() ;                                // Required length of buffer
    if ( len++ )                                           // Check string length, set buffer length
    {
      char buf [ len ] ;                                   // Need some buffer space
      p->str.toCharArray ( buf, len ) ;                    // Make a local copy of the string
      utf8ascii_ip ( buf ) ;                               // Convert possible UTF8
      dsp_setTextColor ( p->color ) ;                      // Set the requested color
      dsp_setCursor ( 0, p->y ) ;                          // Prepare to show the info
      dsp_println ( buf ) ;                                // Show the string
    }
  }
}
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
